UnsicentificLaLaLaLa/led-matrix/software/firmware/led-matrix_firmware/device/mm32g0001a.h

/*
 * Copyright 2023 MindMotion Microelectronics Co., Ltd.
 * All rights reserved.
 *
 * SPDX-License-Identifier: BSD-3-Clause
 */


#ifndef __MM32G0001A_H__
#define __MM32G0001A_H__

#ifdef __cplusplus
extern "C" {
#endif

/* -----------------------------------------------------------------------------
  -- Interrupt vector numbers
  ----------------------------------------------------------------------------- */

/*!
* @addtogroup Interrupt_vector_numbers Interrupt vector numbers

* @{
*/

/** Interrupt Number Definitions */

#define NUMBER_OF_INT_VECTORS 26                 /**< Number of interrupts in the Vector table */

typedef enum IRQ {
    Reset_IRQn                          = -15,                                   /*!< reset */
    NMI_IRQn                            = -14,                                   /*!< Non-Maskable Interrupt/RCC Clock Security System (CSS) connected to NMI vector */
    Hardwarefault_IRQn                  = -13,                                   /*!< All types of failures */
    SVCall_IRQn                         = -5,                                    /*!< System service calls via SWI instructions */
    DebugMonitor_IRQn                   = -4,                                    /*!< debug monitor */
    PendSV_IRQn                         = -2,                                    /*!< Suspendable system services */
    SysTick_IRQn                        = -1,                                    /*!< System tick timer */
    IWDG_IRQn                           = 0,                                     /*!< Watchdog interrupt (IWDG is EXTI17) */
    PVD_IRQn                            = 1,                                     /*!< Supply Voltage Detect (PVD) Interrupt (EXTI16) */
    FLASH_IRQn                          = 3,                                     /*!< Flash Global Interrupt */
    RCC_IRQn                            = 4,                                     /*!< RCC  global interrupt */
    EXTI0_1_IRQn                        = 5,                                     /*!< EXTI line [1: 0] interrupt */
    EXTI2_3_IRQn                        = 6,                                     /*!< EXTI line [3: 2] interrupt */
    EXTI4_15_IRQn                       = 7,                                     /*!< EXTI line [15: 4] interrupt */
    ADC1_IRQn                           = 12,                                    /*!< ADC1 global interrupt */
    TIM1_BRK_UP_TRG_COM_IRQn            = 13,                                    /*!< TIM1 brake, update, trigger, and COM interrupt */
    TIM1_CC_IRQn                        = 14,                                    /*!< TIM1 capture compare interrupt */
    TIM3_IRQn                           = 16,                                    /*!< TIM3 global interrupt */
    TIM14_IRQn                          = 19,                                    /*!< TIM14 global interrupt */
    I2C1_IRQn                           = 23,                                    /*!< I2C1 global interrupt */
    SPI1_IRQn                           = 25,                                    /*!< SPI1 global interrupt */
    USART1_IRQn                         = 27,                                    /*!< USART1 global interrupt */
    USART2_IRQn                         = 28,                                    /*!< USART2 global interrupt */

} IRQn_Type;

/*!

 * @}
 */ /* end of group Interrupt_vector_numbers */


/* -----------------------------------------------------------------------------
 -- Cortex M0 Core Configuration
  ----------------------------------------------------------------------------- */

/*!
 * @addtogroup Cortex_Core_Configuration Cortex M0 Core Configuration
 * @{
 */
#define __CM0_REV                 0x0000U   /* Core revision r0p0 */
#define __MPU_PRESENT             0U        /* no MPU present */
#define __VTOR_PRESENT            0U        /* no VTOR present */
#define __NVIC_PRIO_BITS          2U        /* Number of Bits used for Priority Levels */
#define __Vendor_SysTickConfig    0U        /* Set to 1 if different SysTick Config is used */

#include "core_cm0.h"                /* Core Peripheral Access Layer */

/*!
 * @}
 */ /* end of group Cortex_Core_Configuration */



/* -----------------------------------------------------------------------------
   -- Device Peripheral Access Layer
   ----------------------------------------------------------------------------- */

/*!
 * @addtogroup Peripheral_access_layer Device Peripheral Access Layer
 * @{

 */

/*
** Start of section using anonymous unions
*/

#if   defined (__CC_ARM)
  #pragma push
  #pragma anon_unions
#elif defined (__ICCARM__)
  #pragma language=extended
#elif defined(__ARMCC_VERSION) && (__ARMCC_VERSION >= 6010050)
  #pragma clang diagnostic push
  #pragma clang diagnostic ignored "-Wc11-extensions"
  #pragma clang diagnostic ignored "-Wreserved-id-macro"
#elif defined (__GNUC__)
  /* anonymous unions are enabled by default */
#else
  #warning Not supported compiler type
#endif

/* Define the base address of the large memory block mapping */

#define BOOT_BASE                   0x00000000u
#define FLASH_ADDR_BASE             0x08000000u
#define SYSTEMMEMORY_BASE           0x1FFFF400u
#define OPTIONBYTES_BASE            0x1FFFF800u
#define SRAM_BASE                   0x20000000u
#define APB1_0_BASE                 0x40000000u
#define APB1_1_BASE                 0x40010000u
#define AHB_0_BASE                  0x40020000u
#define AHB_1_BASE                  0x48000000u


/* Define the mapping base address of the peripheral module */
#define TIM3_BASE                   (APB1_0_BASE + 0x0400)
#define IWDG_BASE                   (APB1_0_BASE + 0x3000)
#define USART2_BASE                 (APB1_0_BASE + 0x4400)
#define I2C1_BASE                   (APB1_0_BASE + 0x5400)
#define PWR_BASE                    (APB1_0_BASE + 0x7000)

#define SYSCFG_BASE                 (APB1_1_BASE + 0x0000)
#define EXTI_BASE                   (APB1_1_BASE + 0x0400)
#define ADC1_BASE                   (APB1_1_BASE + 0x2400)
#define TIM1_BASE                   (APB1_1_BASE + 0x2C00)
#define SPI1_BASE                   (APB1_1_BASE + 0x3000)
#define DBGMCU_BASE                 (APB1_1_BASE + 0x3400)
#define USART1_BASE                 (APB1_1_BASE + 0x3800)
#define TIM14_BASE                  (APB1_1_BASE + 0x4000)

#define RCC_BASE                    (AHB_0_BASE + 0x1000)
#define FLASH_BASE                  (AHB_0_BASE + 0x2000)
#define CRC_BASE                    (AHB_0_BASE + 0x3000)

#define GPIOA_BASE                  (AHB_1_BASE + 0x0000)
#define GPIOB_BASE                  (AHB_1_BASE + 0x0400)



/*!
 * @addtogroup ADC_Peripheral_Access_Layer ADC Peripheral Access Layer
 *  @{
 */

/*******************************************************************************
 * ADC Type
 ******************************************************************************/
typedef struct {
    __IO uint32_t ADDATA;                                                         ///< Data register                                offset: 0x00
    __IO uint32_t ADCFG;                                                         ///< Configure register                           offset: 0x04
    __IO uint32_t ADCR;                                                           ///< Control register                             offset: 0x08
    __IO uint32_t Reserved0[1];                                                   ///< Reserved
    __IO uint32_t ADCMPR;                                                         ///< Compare register                             offset: 0x10
    __IO uint32_t ADSTA;                                                          ///< Status register                              offset: 0x14
    __IO uint32_t ADDR[9];                                                        ///< Channel data register                        offset: 0x18
    __IO uint32_t Reserved1[8];                                                   ///< Reserved
    __IO uint32_t CHANY0;                                                         ///< Arbitrary channel channel selection register 0offset: 0x5C
    __IO uint32_t CHANY1;                                                         ///< Arbitrary channel channel selection register 1offset: 0x60
    __IO uint32_t ANYCFG;                                                         ///< Arbitrary channel configuration register     offset: 0x64
    __IO uint32_t ANYCR;                                                          ///< Arbitrary channel control register           offset: 0x68
} ADC_Type;

/*!
 * @addtogroup ADC_Register_Masks Register Masks
 * @{ */

/*!
 * @brief ADC_ADDATA Register Bit Definition
 */

#define ADC_ADDATA_VALID_SHIFT                          (21)
#define ADC_ADDATA_VALID_MASK                           (0x01U << ADC_ADDATA_VALID_SHIFT)
#define ADC_ADDATA_VALID(x)                             (((uint32_t)(((uint32_t)(x)) << ADC_ADDATA_VALID_SHIFT)) & ADC_ADDATA_VALID_MASK)

#define ADC_ADDATA_OVERRUN_SHIFT                        (20)
#define ADC_ADDATA_OVERRUN_MASK                         (0x01U << ADC_ADDATA_OVERRUN_SHIFT)
#define ADC_ADDATA_OVERRUN(x)                           (((uint32_t)(((uint32_t)(x)) << ADC_ADDATA_OVERRUN_SHIFT)) & ADC_ADDATA_OVERRUN_MASK)

#define ADC_ADDATA_CHANNELSEL_SHIFT                     (16)
#define ADC_ADDATA_CHANNELSEL_MASK                      (0x0FU << ADC_ADDATA_CHANNELSEL_SHIFT)
#define ADC_ADDATA_CHANNELSEL(x)                        (((uint32_t)(((uint32_t)(x)) << ADC_ADDATA_CHANNELSEL_SHIFT)) & ADC_ADDATA_CHANNELSEL_MASK)

#define ADC_ADDATA_DATA_SHIFT                           (0)
#define ADC_ADDATA_DATA_MASK                            (0xFFFFU << ADC_ADDATA_DATA_SHIFT)
#define ADC_ADDATA_DATA(x)                              (((uint32_t)(((uint32_t)(x)) << ADC_ADDATA_DATA_SHIFT)) & ADC_ADDATA_DATA_MASK)

/*!
 * @brief ADC_ADCFG Register Bit Definition
 */

#define ADC_ADCFG_ADCPREL_SHIFT                        (14)
#define ADC_ADCFG_ADCPREL_MASK                         (0x01U << ADC_ADCFG_ADCPREL_SHIFT)
#define ADC_ADCFG_ADCPREL(x)                           (((uint32_t)(((uint32_t)(x)) << ADC_ADCFG_ADCPREL_SHIFT)) & ADC_ADCFG_ADCPREL_MASK)

#define ADC_ADCFG_SAMCTL_SHIFT                         (10)
#define ADC_ADCFG_SAMCTL_MASK                          (0x0FU << ADC_ADCFG_SAMCTL_SHIFT)
#define ADC_ADCFG_SAMCTL(x)                            (((uint32_t)(((uint32_t)(x)) << ADC_ADCFG_SAMCTL_SHIFT)) & ADC_ADCFG_SAMCTL_MASK)

#define ADC_ADCFG_RSLTCTL_SHIFT                        (7)
#define ADC_ADCFG_RSLTCTL_MASK                         (0x07U << ADC_ADCFG_RSLTCTL_SHIFT)
#define ADC_ADCFG_RSLTCTL(x)                           (((uint32_t)(((uint32_t)(x)) << ADC_ADCFG_RSLTCTL_SHIFT)) & ADC_ADCFG_RSLTCTL_MASK)

#define ADC_ADCFG_ADCPREH_SHIFT                        (4)
#define ADC_ADCFG_ADCPREH_MASK                         (0x07U << ADC_ADCFG_ADCPREH_SHIFT)
#define ADC_ADCFG_ADCPREH(x)                           (((uint32_t)(((uint32_t)(x)) << ADC_ADCFG_ADCPREH_SHIFT)) & ADC_ADCFG_ADCPREH_MASK)

#define ADC_ADCFG_VSEN_SHIFT                           (3)
#define ADC_ADCFG_VSEN_MASK                            (0x01U << ADC_ADCFG_VSEN_SHIFT)
#define ADC_ADCFG_VSEN(x)                              (((uint32_t)(((uint32_t)(x)) << ADC_ADCFG_VSEN_SHIFT)) & ADC_ADCFG_VSEN_MASK)

#define ADC_ADCFG_AWDEN_SHIFT                          (1)
#define ADC_ADCFG_AWDEN_MASK                           (0x01U << ADC_ADCFG_AWDEN_SHIFT)
#define ADC_ADCFG_AWDEN(x)                             (((uint32_t)(((uint32_t)(x)) << ADC_ADCFG_AWDEN_SHIFT)) & ADC_ADCFG_AWDEN_MASK)

#define ADC_ADCFG_ADEN_SHIFT                           (0)
#define ADC_ADCFG_ADEN_MASK                            (0x01U << ADC_ADCFG_ADEN_SHIFT)
#define ADC_ADCFG_ADEN(x)                              (((uint32_t)(((uint32_t)(x)) << ADC_ADCFG_ADEN_SHIFT)) & ADC_ADCFG_ADEN_MASK)

/*!
 * @brief ADC_ADCR Register Bit Definition
 */

#define ADC_ADCR_TRGEDGE_SHIFT                          (24)
#define ADC_ADCR_TRGEDGE_MASK                           (0x03U << ADC_ADCR_TRGEDGE_SHIFT)
#define ADC_ADCR_TRGEDGE(x)                             (((uint32_t)(((uint32_t)(x)) << ADC_ADCR_TRGEDGE_SHIFT)) & ADC_ADCR_TRGEDGE_MASK)

#define ADC_ADCR_TRGSHIFT_SHIFT                         (19)
#define ADC_ADCR_TRGSHIFT_MASK                          (0x07U << ADC_ADCR_TRGSHIFT_SHIFT)
#define ADC_ADCR_TRGSHIFT(x)                            (((uint32_t)(((uint32_t)(x)) << ADC_ADCR_TRGSHIFT_SHIFT)) & ADC_ADCR_TRGSHIFT_MASK)

#define ADC_ADCR_TRGSELH_SHIFT                          (17)
#define ADC_ADCR_TRGSELH_MASK                           (0x03U << ADC_ADCR_TRGSELH_SHIFT)
#define ADC_ADCR_TRGSELH(x)                             (((uint32_t)(((uint32_t)(x)) << ADC_ADCR_TRGSELH_SHIFT)) & ADC_ADCR_TRGSELH_MASK)

#define ADC_ADCR_CMPCH_SHIFT                            (12)
#define ADC_ADCR_CMPCH_MASK                             (0x0FU << ADC_ADCR_CMPCH_SHIFT)
#define ADC_ADCR_CMPCH(x)                               (((uint32_t)(((uint32_t)(x)) << ADC_ADCR_CMPCH_SHIFT)) & ADC_ADCR_CMPCH_MASK)

#define ADC_ADCR_ALIGN_SHIFT                            (11)
#define ADC_ADCR_ALIGN_MASK                             (0x01U << ADC_ADCR_ALIGN_SHIFT)
#define ADC_ADCR_ALIGN(x)                               (((uint32_t)(((uint32_t)(x)) << ADC_ADCR_ALIGN_SHIFT)) & ADC_ADCR_ALIGN_MASK)

#define ADC_ADCR_ADMD_SHIFT                             (9)
#define ADC_ADCR_ADMD_MASK                              (0x03U << ADC_ADCR_ADMD_SHIFT)
#define ADC_ADCR_ADMD(x)                                (((uint32_t)(((uint32_t)(x)) << ADC_ADCR_ADMD_SHIFT)) & ADC_ADCR_ADMD_MASK)

#define ADC_ADCR_ADST_SHIFT                             (8)
#define ADC_ADCR_ADST_MASK                              (0x01U << ADC_ADCR_ADST_SHIFT)
#define ADC_ADCR_ADST(x)                                (((uint32_t)(((uint32_t)(x)) << ADC_ADCR_ADST_SHIFT)) & ADC_ADCR_ADST_MASK)

#define ADC_ADCR_TRGSELL_SHIFT                          (4)
#define ADC_ADCR_TRGSELL_MASK                           (0x07U << ADC_ADCR_TRGSELL_SHIFT)
#define ADC_ADCR_TRGSELL(x)                             (((uint32_t)(((uint32_t)(x)) << ADC_ADCR_TRGSELL_SHIFT)) & ADC_ADCR_TRGSELL_MASK)

#define ADC_ADCR_TRGEN_SHIFT                            (2)
#define ADC_ADCR_TRGEN_MASK                             (0x01U << ADC_ADCR_TRGEN_SHIFT)
#define ADC_ADCR_TRGEN(x)                               (((uint32_t)(((uint32_t)(x)) << ADC_ADCR_TRGEN_SHIFT)) & ADC_ADCR_TRGEN_MASK)

#define ADC_ADCR_AWDIE_SHIFT                            (1)
#define ADC_ADCR_AWDIE_MASK                             (0x01U << ADC_ADCR_AWDIE_SHIFT)
#define ADC_ADCR_AWDIE(x)                               (((uint32_t)(((uint32_t)(x)) << ADC_ADCR_AWDIE_SHIFT)) & ADC_ADCR_AWDIE_MASK)

#define ADC_ADCR_ADIE_SHIFT                             (0)
#define ADC_ADCR_ADIE_MASK                              (0x01U << ADC_ADCR_ADIE_SHIFT)
#define ADC_ADCR_ADIE(x)                                (((uint32_t)(((uint32_t)(x)) << ADC_ADCR_ADIE_SHIFT)) & ADC_ADCR_ADIE_MASK)

/*!
 * @brief ADC_ADCMPR Register Bit Definition
 */

#define ADC_ADCMPR_CMPHDATA_SHIFT                       (16)
#define ADC_ADCMPR_CMPHDATA_MASK                        (0xFFFU << ADC_ADCMPR_CMPHDATA_SHIFT)
#define ADC_ADCMPR_CMPHDATA(x)                          (((uint32_t)(((uint32_t)(x)) << ADC_ADCMPR_CMPHDATA_SHIFT)) & ADC_ADCMPR_CMPHDATA_MASK)

#define ADC_ADCMPR_CMPLDATA_SHIFT                       (0)
#define ADC_ADCMPR_CMPLDATA_MASK                        (0xFFFU << ADC_ADCMPR_CMPLDATA_SHIFT)
#define ADC_ADCMPR_CMPLDATA(x)                          (((uint32_t)(((uint32_t)(x)) << ADC_ADCMPR_CMPLDATA_SHIFT)) & ADC_ADCMPR_CMPLDATA_MASK)

/*!
 * @brief ADC_ADSTA Register Bit Definition
 */

#define ADC_ADSTA_OVERRUN_SHIFT                         (20)
#define ADC_ADSTA_OVERRUN_MASK                          (0x3FFU << ADC_ADSTA_OVERRUN_SHIFT)
#define ADC_ADSTA_OVERRUN(x)                            (((uint32_t)(((uint32_t)(x)) << ADC_ADSTA_OVERRUN_SHIFT)) & ADC_ADSTA_OVERRUN_MASK)

#define ADC_ADSTA_VALID_SHIFT                           (8)
#define ADC_ADSTA_VALID_MASK                            (0x1FFU << ADC_ADSTA_VALID_SHIFT)
#define ADC_ADSTA_VALID(x)                              (((uint32_t)(((uint32_t)(x)) << ADC_ADSTA_VALID_SHIFT)) & ADC_ADSTA_VALID_MASK)

#define ADC_ADSTA_CH_SHIFT                              (4)
#define ADC_ADSTA_CH_MASK                               (0x0FU << ADC_ADSTA_CH_SHIFT)
#define ADC_ADSTA_CH(x)                                 (((uint32_t)(((uint32_t)(x)) << ADC_ADSTA_CH_SHIFT)) & ADC_ADSTA_CH_MASK)

#define ADC_ADSTA_BUSY_SHIFT                            (2)
#define ADC_ADSTA_BUSY_MASK                             (0x01U << ADC_ADSTA_BUSY_SHIFT)
#define ADC_ADSTA_BUSY(x)                               (((uint32_t)(((uint32_t)(x)) << ADC_ADSTA_BUSY_SHIFT)) & ADC_ADSTA_BUSY_MASK)

#define ADC_ADSTA_AWDIF_SHIFT                           (1)
#define ADC_ADSTA_AWDIF_MASK                            (0x01U << ADC_ADSTA_AWDIF_SHIFT)
#define ADC_ADSTA_AWDIF(x)                              (((uint32_t)(((uint32_t)(x)) << ADC_ADSTA_AWDIF_SHIFT)) & ADC_ADSTA_AWDIF_MASK)

#define ADC_ADSTA_ADIF_SHIFT                            (0)
#define ADC_ADSTA_ADIF_MASK                             (0x01U << ADC_ADSTA_ADIF_SHIFT)
#define ADC_ADSTA_ADIF(x)                               (((uint32_t)(((uint32_t)(x)) << ADC_ADSTA_ADIF_SHIFT)) & ADC_ADSTA_ADIF_MASK)

/*!
 * @brief ADC_ADDR Register Bit Definition
 */

#define ADC_ADDR_VALID_SHIFT                            (21)
#define ADC_ADDR_VALID_MASK                             (0x01U << ADC_ADDR_VALID_SHIFT)
#define ADC_ADDR_VALID(x)                               (((uint32_t)(((uint32_t)(x)) << ADC_ADDR_VALID_SHIFT)) & ADC_ADDR_VALID_MASK)
#define ADC_ADDR_OVERRUN_SHIFT                          (20)
#define ADC_ADDR_OVERRUN_MASK                           (0x01U << ADC_ADDR_OVERRUN_SHIFT)
#define ADC_ADDR_OVERRUN(x)                             (((uint32_t)(((uint32_t)(x)) << ADC_ADDR_OVERRUN_SHIFT)) & ADC_ADDR_OVERRUN_MASK)
#define ADC_ADDR_DATA_SHIFT                             (0)
#define ADC_ADDR_DATA_MASK                              (0xFFFFU << ADC_ADDR_DATA_SHIFT)
#define ADC_ADDR_DATA(x)                                (((uint32_t)(((uint32_t)(x)) << ADC_ADDR_DATA_SHIFT)) & ADC_ADDR_DATA_MASK)

/*!
 * @brief ADC_CHANY0 Register Bit Definition
 */

#define ADC_CHANY0_CHANYSEL7_SHIFT                      (28)
#define ADC_CHANY0_CHANYSEL7_MASK                       (0x0FU << ADC_CHANY0_CHANYSEL7_SHIFT)
#define ADC_CHANY0_CHANYSEL7(x)                         (((uint32_t)(((uint32_t)(x)) << ADC_CHANY0_CHANYSEL7_SHIFT)) & ADC_CHANY0_CHANYSEL7_MASK)

#define ADC_CHANY0_CHANYSEL6_SHIFT                      (24)
#define ADC_CHANY0_CHANYSEL6_MASK                       (0x0FU << ADC_CHANY0_CHANYSEL6_SHIFT)
#define ADC_CHANY0_CHANYSEL6(x)                         (((uint32_t)(((uint32_t)(x)) << ADC_CHANY0_CHANYSEL6_SHIFT)) & ADC_CHANY0_CHANYSEL6_MASK)

#define ADC_CHANY0_CHANYSEL5_SHIFT                      (20)
#define ADC_CHANY0_CHANYSEL5_MASK                       (0x0FU << ADC_CHANY0_CHANYSEL5_SHIFT)
#define ADC_CHANY0_CHANYSEL5(x)                         (((uint32_t)(((uint32_t)(x)) << ADC_CHANY0_CHANYSEL5_SHIFT)) & ADC_CHANY0_CHANYSEL5_MASK)

#define ADC_CHANY0_CHANYSEL4_SHIFT                      (16)
#define ADC_CHANY0_CHANYSEL4_MASK                       (0x0FU << ADC_CHANY0_CHANYSEL4_SHIFT)
#define ADC_CHANY0_CHANYSEL4(x)                         (((uint32_t)(((uint32_t)(x)) << ADC_CHANY0_CHANYSEL4_SHIFT)) & ADC_CHANY0_CHANYSEL4_MASK)

#define ADC_CHANY0_CHANYSEL3_SHIFT                      (12)
#define ADC_CHANY0_CHANYSEL3_MASK                       (0x0FU << ADC_CHANY0_CHANYSEL3_SHIFT)
#define ADC_CHANY0_CHANYSEL3(x)                         (((uint32_t)(((uint32_t)(x)) << ADC_CHANY0_CHANYSEL3_SHIFT)) & ADC_CHANY0_CHANYSEL3_MASK)

#define ADC_CHANY0_CHANYSEL2_SHIFT                      (8)
#define ADC_CHANY0_CHANYSEL2_MASK                       (0x0FU << ADC_CHANY0_CHANYSEL2_SHIFT)
#define ADC_CHANY0_CHANYSEL2(x)                         (((uint32_t)(((uint32_t)(x)) << ADC_CHANY0_CHANYSEL2_SHIFT)) & ADC_CHANY0_CHANYSEL2_MASK)

#define ADC_CHANY0_CHANYSEL1_SHIFT                      (4)
#define ADC_CHANY0_CHANYSEL1_MASK                       (0x0FU << ADC_CHANY0_CHANYSEL1_SHIFT)
#define ADC_CHANY0_CHANYSEL1(x)                         (((uint32_t)(((uint32_t)(x)) << ADC_CHANY0_CHANYSEL1_SHIFT)) & ADC_CHANY0_CHANYSEL1_MASK)

#define ADC_CHANY0_CHANYSEL0_SHIFT                      (0)
#define ADC_CHANY0_CHANYSEL0_MASK                       (0x0FU << ADC_CHANY0_CHANYSEL0_SHIFT)
#define ADC_CHANY0_CHANYSEL0(x)                         (((uint32_t)(((uint32_t)(x)) << ADC_CHANY0_CHANYSEL0_SHIFT)) & ADC_CHANY0_CHANYSEL0_MASK)

/*!
 * @brief ADC_CHANY1 Register Bit Definition
 */

#define ADC_CHANY1_CHANYSEL8_SHIFT                      (0)
#define ADC_CHANY1_CHANYSEL8_MASK                       (0x0FU << ADC_CHANY1_CHANYSEL8_SHIFT)
#define ADC_CHANY1_CHANYSEL8(x)                         (((uint32_t)(((uint32_t)(x)) << ADC_CHANY1_CHANYSEL8_SHIFT)) & ADC_CHANY1_CHANYSEL8_MASK)

/*!
 * @brief ADC_ANYCFG Register Bit Definition
 */

#define ADC_ANYCFG_CHANYNUM_SHIFT                      (0)
#define ADC_ANYCFG_CHANYNUM_MASK                       (0x0FU << ADC_ANYCFG_CHANYNUM_SHIFT)
#define ADC_ANYCFG_CHANYNUM(x)                         (((uint32_t)(((uint32_t)(x)) << ADC_ANYCFG_CHANYNUM_SHIFT)) & ADC_ANYCFG_CHANYNUM_MASK)

/*!
 * @brief ADC_ANYCR Register Bit Definition
 */

#define ADC_ANYCR_CHANYMDEN_SHIFT                      (0)
#define ADC_ANYCR_CHANYMDEN_MASK                       (0x01U << ADC_ANYCR_CHANYMDEN_SHIFT)
#define ADC_ANYCR_CHANYMDEN(x)                         (((uint32_t)(((uint32_t)(x)) << ADC_ANYCR_CHANYMDEN_SHIFT)) & ADC_ANYCR_CHANYMDEN_MASK)

/*!
 * @}
 */ /* end of group ADC_Register_Masks */
/******************************************************************************
 * ADC Instance
 ******************************************************************************/

#define ADC1                ((ADC_Type*)ADC1_BASE)

/*!
 * @}
 */ /* end of group ADC_Peripheral_Access_Layer */

/*!
 * @addtogroup CRC_Peripheral_Access_Layer CRC Peripheral Access Layer
 *  @{
 */

/*******************************************************************************
 * CRC Type
 ******************************************************************************/
typedef struct {
    __IO uint32_t DR;                                                             ///< Data register                                offset: 0x00
    __IO uint32_t IDR;                                                            ///< Independent data register                    offset: 0x04
    __IO uint32_t CTRL;                                                           ///< Control register                             offset: 0x08
} CRC_Type;

/*!
 * @addtogroup CRC_Register_Masks Register Masks
 * @{ */

/*!
 * @brief CRC_DR Register Bit Definition
 */

#define CRC_DR_DR_SHIFT                                 (0)
#define CRC_DR_DR_MASK                                  (0xFFFFFFFFU << CRC_DR_DR_SHIFT)
#define CRC_DR_DR(x)                                    (((uint32_t)(((uint32_t)(x)) << CRC_DR_DR_SHIFT)) & CRC_DR_DR_MASK)

/*!
 * @brief CRC_IDR Register Bit Definition
 */

#define CRC_IDR_IDR_SHIFT                               (0)
#define CRC_IDR_IDR_MASK                                (0xFFU << CRC_IDR_IDR_SHIFT)
#define CRC_IDR_IDR(x)                                  (((uint32_t)(((uint32_t)(x)) << CRC_IDR_IDR_SHIFT)) & CRC_IDR_IDR_MASK)

/*!
 * @brief CRC_CTRL Register Bit Definition
 */

#define CRC_CTRL_RESET_SHIFT                            (0)
#define CRC_CTRL_RESET_MASK                             (0x01U << CRC_CTRL_RESET_SHIFT)
#define CRC_CTRL_RESET(x)                               (((uint32_t)(((uint32_t)(x)) << CRC_CTRL_RESET_SHIFT)) & CRC_CTRL_RESET_MASK)

/*!
 * @}
 */ /* end of group CRC_Register_Masks */
/******************************************************************************
 * CRC Instance
 ******************************************************************************/

#define CRC                ((CRC_Type*)CRC_BASE)

/*!
 * @}
 */ /* end of group CRC_Peripheral_Access_Layer */

/*!
 * @addtogroup DBGMCU_Peripheral_Access_Layer DBG Peripheral Access Layer
 *  @{
 */

/*******************************************************************************
 * DBGMCU Type
 ******************************************************************************/
typedef struct {
    __IO uint32_t IDCODE;                                                         ///< ID CODE                                      offset: 0x00
    __IO uint32_t CR;                                                             ///< Control Register                             offset: 0x04
} DBGMCU_Type;

/*!
 * @addtogroup DBGMCU_Register_Masks Register Masks
 * @{ */

/*!
 * @brief DBGMCU_IDCODE Register Bit Definition
 */

#define DBGMCU_IDCODE_DEVID_SHIFT                          (0)
#define DBGMCU_IDCODE_DEVID_MASK                           (0xFFFFFFFFU << DBGMCU_IDCODE_DEVID_SHIFT)
#define DBGMCU_IDCODE_DEVID(x)                             (((uint32_t)(((uint32_t)(x)) << DBGMCU_IDCODE_DEVID_SHIFT)) & DBGMCU_IDCODE_DEVID_MASK)

/*!
 * @brief DBGMCU_CR Register Bit Definition
 */

#define DBGMCU_CR_DBGTIM14STOP_SHIFT                       (18)
#define DBGMCU_CR_DBGTIM14STOP_MASK                        (0x01U << DBGMCU_CR_DBGTIM14STOP_SHIFT)
#define DBGMCU_CR_DBGTIM14STOP(x)                          (((uint32_t)(((uint32_t)(x)) << DBGMCU_CR_DBGTIM14STOP_SHIFT)) & DBGMCU_CR_DBGTIM14STOP_MASK)

#define DBGMCU_CR_DBGTIM3PWMOFF_SHIFT                      (15)
#define DBGMCU_CR_DBGTIM3PWMOFF_MASK                       (0x01U << DBGMCU_CR_DBGTIM3PWMOFF_SHIFT)
#define DBGMCU_CR_DBGTIM3PWMOFF(x)                         (((uint32_t)(((uint32_t)(x)) << DBGMCU_CR_DBGTIM3PWMOFF_SHIFT)) & DBGMCU_CR_DBGTIM3PWMOFF_MASK)

#define DBGMCU_CR_DBGTIM1PWMOFF_SHIFT                      (13)
#define DBGMCU_CR_DBGTIM1PWMOFF_MASK                       (0x01U << DBGMCU_CR_DBGTIM1PWMOFF_SHIFT)
#define DBGMCU_CR_DBGTIM1PWMOFF(x)                         (((uint32_t)(((uint32_t)(x)) << DBGMCU_CR_DBGTIM1PWMOFF_SHIFT)) & DBGMCU_CR_DBGTIM1PWMOFF_MASK)

#define DBGMCU_CR_DBGTIM3STOP_SHIFT                        (12)
#define DBGMCU_CR_DBGTIM3STOP_MASK                         (0x01U << DBGMCU_CR_DBGTIM3STOP_SHIFT)
#define DBGMCU_CR_DBGTIM3STOP(x)                           (((uint32_t)(((uint32_t)(x)) << DBGMCU_CR_DBGTIM3STOP_SHIFT)) & DBGMCU_CR_DBGTIM3STOP_MASK)

#define DBGMCU_CR_DBGTIM1STOP_SHIFT                        (10)
#define DBGMCU_CR_DBGTIM1STOP_MASK                         (0x01U << DBGMCU_CR_DBGTIM1STOP_SHIFT)
#define DBGMCU_CR_DBGTIM1STOP(x)                           (((uint32_t)(((uint32_t)(x)) << DBGMCU_CR_DBGTIM1STOP_SHIFT)) & DBGMCU_CR_DBGTIM1STOP_MASK)

#define DBGMCU_CR_DBGIWDGSTOP_SHIFT                        (8)
#define DBGMCU_CR_DBGIWDGSTOP_MASK                         (0x01U << DBGMCU_CR_DBGIWDGSTOP_SHIFT)
#define DBGMCU_CR_DBGIWDGSTOP(x)                           (((uint32_t)(((uint32_t)(x)) << DBGMCU_CR_DBGIWDGSTOP_SHIFT)) & DBGMCU_CR_DBGIWDGSTOP_MASK)

#define DBGMCU_CR_DBGSTOPFORLDO_SHIFT                      (3)
#define DBGMCU_CR_DBGSTOPFORLDO_MASK                       (0x01U << DBGMCU_CR_DBGSTOPFORLDO_SHIFT)
#define DBGMCU_CR_DBGSTOPFORLDO(x)                         (((uint32_t)(((uint32_t)(x)) << DBGMCU_CR_DBGSTOPFORLDO_SHIFT)) & DBGMCU_CR_DBGSTOPFORLDO_MASK)

#define DBGMCU_CR_DBGSTOP_SHIFT                            (1)
#define DBGMCU_CR_DBGSTOP_MASK                             (0x01U << DBGMCU_CR_DBGSTOP_SHIFT)
#define DBGMCU_CR_DBGSTOP(x)                               (((uint32_t)(((uint32_t)(x)) << DBGMCU_CR_DBGSTOP_SHIFT)) & DBGMCU_CR_DBGSTOP_MASK)

#define DBGMCU_CR_DBGSLEEP_SHIFT                           (0)
#define DBGMCU_CR_DBGSLEEP_MASK                            (0x01U << DBGMCU_CR_DBGSLEEP_SHIFT)
#define DBGMCU_CR_DBGSLEEP(x)                              (((uint32_t)(((uint32_t)(x)) << DBGMCU_CR_DBGSLEEP_SHIFT)) & DBGMCU_CR_DBGSLEEP_MASK)

/*!
 * @}
 */ /* end of group DBGMCU_Register_Masks */
/******************************************************************************
 * DBGMCU Instance
 ******************************************************************************/

#define DBGMCU                ((DBGMCU_Type*)DBGMCU_BASE)

/*!
 * @}
 */ /* end of group DBGMCU_Peripheral_Access_Layer */

/*!
 * @addtogroup DEVICE_Peripheral_Access_Layer DEVICE Peripheral Access Layer
 *  @{
 */

/*******************************************************************************
 * DEVICE Type
 ******************************************************************************/
typedef struct {
    __IO uint32_t UID1;                                                           ///< Configuration register                       offset: 0x00
    __IO uint32_t UID2;                                                           ///< Configuration register                       offset: 0x04
    __IO uint32_t UID3;                                                           ///< Configuration register                       offset: 0x08
} DEVICE_Type;

/*!
 * @addtogroup DEVICE_Register_Masks Register Masks
 * @{ */

/*!
 * @brief DEVICE_UID1 Register Bit Definition
 */

#define DEVICE_UID1_UID_SHIFT                           (0)
#define DEVICE_UID1_UID_MASK                            (0xFFFFFFFFU << DEVICE_UID1_UID_SHIFT)
#define DEVICE_UID1_UID(x)                              (((uint32_t)(((uint32_t)(x)) << DEVICE_UID1_UID_SHIFT)) & DEVICE_UID1_UID_MASK)

/*!
 * @brief DEVICE_UID2 Register Bit Definition
 */

#define DEVICE_UID2_UID_SHIFT                           (0)
#define DEVICE_UID2_UID_MASK                            (0xFFFFFFFFU << DEVICE_UID2_UID_SHIFT)
#define DEVICE_UID2_UID(x)                              (((uint32_t)(((uint32_t)(x)) << DEVICE_UID2_UID_SHIFT)) & DEVICE_UID2_UID_MASK)

/*!
 * @brief DEVICE_UID3 Register Bit Definition
 */

#define DEVICE_UID3_UID_SHIFT                           (0)
#define DEVICE_UID3_UID_MASK                            (0xFFFFFFFFU << DEVICE_UID3_UID_SHIFT)
#define DEVICE_UID3_UID(x)                              (((uint32_t)(((uint32_t)(x)) << DEVICE_UID3_UID_SHIFT)) & DEVICE_UID3_UID_MASK)

/*!
 * @}
 */ /* end of group DEVICE_Register_Masks */
/******************************************************************************
 * DEVICE Instance
 ******************************************************************************/

#define DEVICE                ((DEVICE_Type*)DEVICE_BASE)

/*!
 * @}
 */ /* end of group DEVICE_Peripheral_Access_Layer */

/*!
 * @addtogroup SYSCFG_Peripheral_Access_Layer SYSCFG Peripheral Access Layer
 *  @{
 */

/*******************************************************************************
 * SYSCFG Type
 ******************************************************************************/
typedef struct {
    __IO uint32_t CFGR;                                                           ///< Configuration register                       offset: 0x00
    __IO uint32_t Reserved0[1];                                                   ///< Reserved
    __IO uint32_t EXTICR1;                                                        ///< External interrupt configuration register 1  offset: 0x08
    __IO uint32_t EXTICR2;                                                        ///< External interrupt configuration register 2  offset: 0x0C
    __IO uint32_t EXTICR3;                                                        ///< External interrupt configuration register 3  offset: 0x10
    __IO uint32_t EXTICR4;                                                        ///< External interrupt configuration register 4  offset: 0x14
    __IO uint32_t PADHYS;                                                         ///< PAD configuration register                   offset: 0x18
} SYSCFG_Type;

/*!
 * @addtogroup SYSCFG_Register_Masks Register Masks
 * @{ */

/*!
 * @brief SYSCFG_CFGR Register Bit Definition
 */

#define SYSCFG_CFGR_MEMMODE_SHIFT                       (0)
#define SYSCFG_CFGR_MEMMODE_MASK                        (0x03U << SYSCFG_CFGR_MEMMODE_SHIFT)
#define SYSCFG_CFGR_MEMMODE(x)                          (((uint32_t)(((uint32_t)(x)) << SYSCFG_CFGR_MEMMODE_SHIFT)) & SYSCFG_CFGR_MEMMODE_MASK)

/*!
 * @brief SYSCFG_EXTICR1 Register Bit Definition
 */

#define SYSCFG_EXTICR1_EXTI3_SHIFT                      (12)
#define SYSCFG_EXTICR1_EXTI3_MASK                       (0x0FU << SYSCFG_EXTICR1_EXTI3_SHIFT)
#define SYSCFG_EXTICR1_EXTI3(x)                         (((uint32_t)(((uint32_t)(x)) << SYSCFG_EXTICR1_EXTI3_SHIFT)) & SYSCFG_EXTICR1_EXTI3_MASK)

#define SYSCFG_EXTICR1_EXTI2_SHIFT                      (8)
#define SYSCFG_EXTICR1_EXTI2_MASK                       (0x0FU << SYSCFG_EXTICR1_EXTI2_SHIFT)
#define SYSCFG_EXTICR1_EXTI2(x)                         (((uint32_t)(((uint32_t)(x)) << SYSCFG_EXTICR1_EXTI2_SHIFT)) & SYSCFG_EXTICR1_EXTI2_MASK)

#define SYSCFG_EXTICR1_EXTI1_SHIFT                      (4)
#define SYSCFG_EXTICR1_EXTI1_MASK                       (0x0FU << SYSCFG_EXTICR1_EXTI1_SHIFT)
#define SYSCFG_EXTICR1_EXTI1(x)                         (((uint32_t)(((uint32_t)(x)) << SYSCFG_EXTICR1_EXTI1_SHIFT)) & SYSCFG_EXTICR1_EXTI1_MASK)

#define SYSCFG_EXTICR1_EXTI0_SHIFT                      (0)
#define SYSCFG_EXTICR1_EXTI0_MASK                       (0x0FU << SYSCFG_EXTICR1_EXTI0_SHIFT)
#define SYSCFG_EXTICR1_EXTI0(x)                         (((uint32_t)(((uint32_t)(x)) << SYSCFG_EXTICR1_EXTI0_SHIFT)) & SYSCFG_EXTICR1_EXTI0_MASK)

/*!
 * @brief SYSCFG_EXTICR2 Register Bit Definition
 */

#define SYSCFG_EXTICR2_EXTI7_SHIFT                      (12)
#define SYSCFG_EXTICR2_EXTI7_MASK                       (0x0FU << SYSCFG_EXTICR2_EXTI7_SHIFT)
#define SYSCFG_EXTICR2_EXTI7(x)                         (((uint32_t)(((uint32_t)(x)) << SYSCFG_EXTICR2_EXTI7_SHIFT)) & SYSCFG_EXTICR2_EXTI7_MASK)

#define SYSCFG_EXTICR2_EXTI6_SHIFT                      (8)
#define SYSCFG_EXTICR2_EXTI6_MASK                       (0x0FU << SYSCFG_EXTICR2_EXTI6_SHIFT)
#define SYSCFG_EXTICR2_EXTI6(x)                         (((uint32_t)(((uint32_t)(x)) << SYSCFG_EXTICR2_EXTI6_SHIFT)) & SYSCFG_EXTICR2_EXTI6_MASK)

#define SYSCFG_EXTICR2_EXTI5_SHIFT                      (4)
#define SYSCFG_EXTICR2_EXTI5_MASK                       (0x0FU << SYSCFG_EXTICR2_EXTI5_SHIFT)
#define SYSCFG_EXTICR2_EXTI5(x)                         (((uint32_t)(((uint32_t)(x)) << SYSCFG_EXTICR2_EXTI5_SHIFT)) & SYSCFG_EXTICR2_EXTI5_MASK)

#define SYSCFG_EXTICR2_EXTI4_SHIFT                      (0)
#define SYSCFG_EXTICR2_EXTI4_MASK                       (0x0FU << SYSCFG_EXTICR2_EXTI4_SHIFT)
#define SYSCFG_EXTICR2_EXTI4(x)                         (((uint32_t)(((uint32_t)(x)) << SYSCFG_EXTICR2_EXTI4_SHIFT)) & SYSCFG_EXTICR2_EXTI4_MASK)

/*!
 * @brief SYSCFG_EXTICR3 Register Bit Definition
 */

#define SYSCFG_EXTICR3_EXTI11_SHIFT                     (12)
#define SYSCFG_EXTICR3_EXTI11_MASK                      (0x0FU << SYSCFG_EXTICR3_EXTI11_SHIFT)
#define SYSCFG_EXTICR3_EXTI11(x)                        (((uint32_t)(((uint32_t)(x)) << SYSCFG_EXTICR3_EXTI11_SHIFT)) & SYSCFG_EXTICR3_EXTI11_MASK)

#define SYSCFG_EXTICR3_EXTI10_SHIFT                     (8)
#define SYSCFG_EXTICR3_EXTI10_MASK                      (0x0FU << SYSCFG_EXTICR3_EXTI10_SHIFT)
#define SYSCFG_EXTICR3_EXTI10(x)                        (((uint32_t)(((uint32_t)(x)) << SYSCFG_EXTICR3_EXTI10_SHIFT)) & SYSCFG_EXTICR3_EXTI10_MASK)

#define SYSCFG_EXTICR3_EXTI9_SHIFT                      (4)
#define SYSCFG_EXTICR3_EXTI9_MASK                       (0x0FU << SYSCFG_EXTICR3_EXTI9_SHIFT)
#define SYSCFG_EXTICR3_EXTI9(x)                         (((uint32_t)(((uint32_t)(x)) << SYSCFG_EXTICR3_EXTI9_SHIFT)) & SYSCFG_EXTICR3_EXTI9_MASK)

#define SYSCFG_EXTICR3_EXTI8_SHIFT                      (0)
#define SYSCFG_EXTICR3_EXTI8_MASK                       (0x0FU << SYSCFG_EXTICR3_EXTI8_SHIFT)
#define SYSCFG_EXTICR3_EXTI8(x)                         (((uint32_t)(((uint32_t)(x)) << SYSCFG_EXTICR3_EXTI8_SHIFT)) & SYSCFG_EXTICR3_EXTI8_MASK)

/*!
 * @brief SYSCFG_EXTICR4 Register Bit Definition
 */

#define SYSCFG_EXTICR4_EXTI15_SHIFT                     (12)
#define SYSCFG_EXTICR4_EXTI15_MASK                      (0x0FU << SYSCFG_EXTICR4_EXTI15_SHIFT)
#define SYSCFG_EXTICR4_EXTI15(x)                        (((uint32_t)(((uint32_t)(x)) << SYSCFG_EXTICR4_EXTI15_SHIFT)) & SYSCFG_EXTICR4_EXTI15_MASK)

#define SYSCFG_EXTICR4_EXTI14_SHIFT                     (8)
#define SYSCFG_EXTICR4_EXTI14_MASK                      (0x0FU << SYSCFG_EXTICR4_EXTI14_SHIFT)
#define SYSCFG_EXTICR4_EXTI14(x)                        (((uint32_t)(((uint32_t)(x)) << SYSCFG_EXTICR4_EXTI14_SHIFT)) & SYSCFG_EXTICR4_EXTI14_MASK)

#define SYSCFG_EXTICR4_EXTI13_SHIFT                     (4)
#define SYSCFG_EXTICR4_EXTI13_MASK                      (0x0FU << SYSCFG_EXTICR4_EXTI13_SHIFT)
#define SYSCFG_EXTICR4_EXTI13(x)                        (((uint32_t)(((uint32_t)(x)) << SYSCFG_EXTICR4_EXTI13_SHIFT)) & SYSCFG_EXTICR4_EXTI13_MASK)

#define SYSCFG_EXTICR4_EXTI12_SHIFT                     (0)
#define SYSCFG_EXTICR4_EXTI12_MASK                      (0x0FU << SYSCFG_EXTICR4_EXTI12_SHIFT)
#define SYSCFG_EXTICR4_EXTI12(x)                        (((uint32_t)(((uint32_t)(x)) << SYSCFG_EXTICR4_EXTI12_SHIFT)) & SYSCFG_EXTICR4_EXTI12_MASK)

/*!
 * @brief SYSCFG_PADHYS Register Bit Definition
 */

#define SYSCFG_PADHYS_I2C1MODESEL_SHIFT                 (16)
#define SYSCFG_PADHYS_I2C1MODESEL_MASK                  (0x01U << SYSCFG_PADHYS_I2C1MODESEL_SHIFT)
#define SYSCFG_PADHYS_I2C1MODESEL(x)                    (((uint32_t)(((uint32_t)(x)) << SYSCFG_PADHYS_I2C1MODESEL_SHIFT)) & SYSCFG_PADHYS_I2C1MODESEL_MASK)

/*!
 * @}
 */ /* end of group SYSCFG_Register_Masks */
/******************************************************************************
 * SYSCFG Instance
 ******************************************************************************/

#define SYSCFG                ((SYSCFG_Type*)SYSCFG_BASE)

/*!
 * @}
 */ /* end of group SYSCFG_Peripheral_Access_Layer */

/*!
 * @addtogroup EXTI_Peripheral_Access_Layer EXTI Peripheral Access Layer
 *  @{
 */

/*******************************************************************************
 * EXTI Type
 ******************************************************************************/
typedef struct {
    __IO uint32_t IMR;                                                            ///< Interrupt mask register                      offset: 0x00
    __IO uint32_t EMR;                                                            ///< Event mask register                          offset: 0x04
    __IO uint32_t RTSR;                                                           ///< Rising trigger selection register            offset: 0x08
    __IO uint32_t FTSR;                                                           ///< Falling trigger selection register           offset: 0x0C
    __IO uint32_t SWIER;                                                          ///< Software interrupt event register            offset: 0x10
    __IO uint32_t PR;                                                             ///< Pending register                             offset: 0x14
} EXTI_Type;

/*!
 * @addtogroup EXTI_Register_Masks Register Masks
 * @{ */

/*!
 * @brief EXTI_IMR Register Bit Definition
 */

#define EXTI_IMR_IMR17_SHIFT                            (17)
#define EXTI_IMR_IMR17_MASK                             (0x01U << EXTI_IMR_IMR17_SHIFT)
#define EXTI_IMR_IMR17(x)                               (((uint32_t)(((uint32_t)(x)) << EXTI_IMR_IMR17_SHIFT)) & EXTI_IMR_IMR17_MASK)

#define EXTI_IMR_IMR16_SHIFT                            (16)
#define EXTI_IMR_IMR16_MASK                             (0x01U << EXTI_IMR_IMR16_SHIFT)
#define EXTI_IMR_IMR16(x)                               (((uint32_t)(((uint32_t)(x)) << EXTI_IMR_IMR16_SHIFT)) & EXTI_IMR_IMR16_MASK)

#define EXTI_IMR_IMR15_SHIFT                            (15)
#define EXTI_IMR_IMR15_MASK                             (0x01U << EXTI_IMR_IMR15_SHIFT)
#define EXTI_IMR_IMR15(x)                               (((uint32_t)(((uint32_t)(x)) << EXTI_IMR_IMR15_SHIFT)) & EXTI_IMR_IMR15_MASK)

#define EXTI_IMR_IMR14_SHIFT                            (14)
#define EXTI_IMR_IMR14_MASK                             (0x01U << EXTI_IMR_IMR14_SHIFT)
#define EXTI_IMR_IMR14(x)                               (((uint32_t)(((uint32_t)(x)) << EXTI_IMR_IMR14_SHIFT)) & EXTI_IMR_IMR14_MASK)

#define EXTI_IMR_IMR13_SHIFT                            (13)
#define EXTI_IMR_IMR13_MASK                             (0x01U << EXTI_IMR_IMR13_SHIFT)
#define EXTI_IMR_IMR13(x)                               (((uint32_t)(((uint32_t)(x)) << EXTI_IMR_IMR13_SHIFT)) & EXTI_IMR_IMR13_MASK)

#define EXTI_IMR_IMR12_SHIFT                            (12)
#define EXTI_IMR_IMR12_MASK                             (0x01U << EXTI_IMR_IMR12_SHIFT)
#define EXTI_IMR_IMR12(x)                               (((uint32_t)(((uint32_t)(x)) << EXTI_IMR_IMR12_SHIFT)) & EXTI_IMR_IMR12_MASK)

#define EXTI_IMR_IMR11_SHIFT                            (11)
#define EXTI_IMR_IMR11_MASK                             (0x01U << EXTI_IMR_IMR11_SHIFT)
#define EXTI_IMR_IMR11(x)                               (((uint32_t)(((uint32_t)(x)) << EXTI_IMR_IMR11_SHIFT)) & EXTI_IMR_IMR11_MASK)

#define EXTI_IMR_IMR10_SHIFT                            (10)
#define EXTI_IMR_IMR10_MASK                             (0x01U << EXTI_IMR_IMR10_SHIFT)
#define EXTI_IMR_IMR10(x)                               (((uint32_t)(((uint32_t)(x)) << EXTI_IMR_IMR10_SHIFT)) & EXTI_IMR_IMR10_MASK)

#define EXTI_IMR_IMR9_SHIFT                             (9)
#define EXTI_IMR_IMR9_MASK                              (0x01U << EXTI_IMR_IMR9_SHIFT)
#define EXTI_IMR_IMR9(x)                                (((uint32_t)(((uint32_t)(x)) << EXTI_IMR_IMR9_SHIFT)) & EXTI_IMR_IMR9_MASK)

#define EXTI_IMR_IMR8_SHIFT                             (8)
#define EXTI_IMR_IMR8_MASK                              (0x01U << EXTI_IMR_IMR8_SHIFT)
#define EXTI_IMR_IMR8(x)                                (((uint32_t)(((uint32_t)(x)) << EXTI_IMR_IMR8_SHIFT)) & EXTI_IMR_IMR8_MASK)

#define EXTI_IMR_IMR7_SHIFT                             (7)
#define EXTI_IMR_IMR7_MASK                              (0x01U << EXTI_IMR_IMR7_SHIFT)
#define EXTI_IMR_IMR7(x)                                (((uint32_t)(((uint32_t)(x)) << EXTI_IMR_IMR7_SHIFT)) & EXTI_IMR_IMR7_MASK)

#define EXTI_IMR_IMR6_SHIFT                             (6)
#define EXTI_IMR_IMR6_MASK                              (0x01U << EXTI_IMR_IMR6_SHIFT)
#define EXTI_IMR_IMR6(x)                                (((uint32_t)(((uint32_t)(x)) << EXTI_IMR_IMR6_SHIFT)) & EXTI_IMR_IMR6_MASK)

#define EXTI_IMR_IMR5_SHIFT                             (5)
#define EXTI_IMR_IMR5_MASK                              (0x01U << EXTI_IMR_IMR5_SHIFT)
#define EXTI_IMR_IMR5(x)                                (((uint32_t)(((uint32_t)(x)) << EXTI_IMR_IMR5_SHIFT)) & EXTI_IMR_IMR5_MASK)

#define EXTI_IMR_IMR4_SHIFT                             (4)
#define EXTI_IMR_IMR4_MASK                              (0x01U << EXTI_IMR_IMR4_SHIFT)
#define EXTI_IMR_IMR4(x)                                (((uint32_t)(((uint32_t)(x)) << EXTI_IMR_IMR4_SHIFT)) & EXTI_IMR_IMR4_MASK)

#define EXTI_IMR_IMR3_SHIFT                             (3)
#define EXTI_IMR_IMR3_MASK                              (0x01U << EXTI_IMR_IMR3_SHIFT)
#define EXTI_IMR_IMR3(x)                                (((uint32_t)(((uint32_t)(x)) << EXTI_IMR_IMR3_SHIFT)) & EXTI_IMR_IMR3_MASK)

#define EXTI_IMR_IMR2_SHIFT                             (2)
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

#define EXTI_PR_PR8_SHIFT                               (8)
#define EXTI_PR_PR8_MASK                                (0x01U << EXTI_PR_PR8_SHIFT)
#define EXTI_PR_PR8(x)                                  (((uint32_t)(((uint32_t)(x)) << EXTI_PR_PR8_SHIFT)) & EXTI_PR_PR8_MASK)

#define EXTI_PR_PR7_SHIFT                               (7)
#define EXTI_PR_PR7_MASK                                (0x01U << EXTI_PR_PR7_SHIFT)
#define EXTI_PR_PR7(x)                                  (((uint32_t)(((uint32_t)(x)) << EXTI_PR_PR7_SHIFT)) & EXTI_PR_PR7_MASK)

#define EXTI_PR_PR6_SHIFT                               (6)
#define EXTI_PR_PR6_MASK                                (0x01U << EXTI_PR_PR6_SHIFT)
#define EXTI_PR_PR6(x)                                  (((uint32_t)(((uint32_t)(x)) << EXTI_PR_PR6_SHIFT)) & EXTI_PR_PR6_MASK)

#define EXTI_PR_PR5_SHIFT                               (5)
#define EXTI_PR_PR5_MASK                                (0x01U << EXTI_PR_PR5_SHIFT)
#define EXTI_PR_PR5(x)                                  (((uint32_t)(((uint32_t)(x)) << EXTI_PR_PR5_SHIFT)) & EXTI_PR_PR5_MASK)

#define EXTI_PR_PR4_SHIFT                               (4)
#define EXTI_PR_PR4_MASK                                (0x01U << EXTI_PR_PR4_SHIFT)
#define EXTI_PR_PR4(x)                                  (((uint32_t)(((uint32_t)(x)) << EXTI_PR_PR4_SHIFT)) & EXTI_PR_PR4_MASK)

#define EXTI_PR_PR3_SHIFT                               (3)
#define EXTI_PR_PR3_MASK                                (0x01U << EXTI_PR_PR3_SHIFT)
#define EXTI_PR_PR3(x)                                  (((uint32_t)(((uint32_t)(x)) << EXTI_PR_PR3_SHIFT)) & EXTI_PR_PR3_MASK)

#define EXTI_PR_PR2_SHIFT                               (2)
#define EXTI_PR_PR2_MASK                                (0x01U << EXTI_PR_PR2_SHIFT)
#define EXTI_PR_PR2(x)                                  (((uint32_t)(((uint32_t)(x)) << EXTI_PR_PR2_SHIFT)) & EXTI_PR_PR2_MASK)

#define EXTI_PR_PR1_SHIFT                               (1)
#define EXTI_PR_PR1_MASK                                (0x01U << EXTI_PR_PR1_SHIFT)
#define EXTI_PR_PR1(x)                                  (((uint32_t)(((uint32_t)(x)) << EXTI_PR_PR1_SHIFT)) & EXTI_PR_PR1_MASK)

#define EXTI_PR_PR0_SHIFT                               (0)
#define EXTI_PR_PR0_MASK                                (0x01U << EXTI_PR_PR0_SHIFT)
#define EXTI_PR_PR0(x)                                  (((uint32_t)(((uint32_t)(x)) << EXTI_PR_PR0_SHIFT)) & EXTI_PR_PR0_MASK)

/*!
 * @}
 */ /* end of group EXTI_Register_Masks */
/******************************************************************************
 * EXTI Instance
 ******************************************************************************/

#define EXTI                ((EXTI_Type*)EXTI_BASE)

/*!
 * @}
 */ /* end of group EXTI_Peripheral_Access_Layer */

/*!
 * @addtogroup FLASH_Peripheral_Access_Layer FLASH Peripheral Access Layer
 *  @{
 */

/*******************************************************************************
 * FLASH Type
 ******************************************************************************/
typedef struct {
    __IO uint32_t ACR;                                                            ///< Flash access control register                offset: 0x00
    __IO uint32_t KEYR;                                                           ///< Flash key                                    offset: 0x04
    __IO uint32_t OPTKEYR;                                                        ///< Option byte key                              offset: 0x08
    __IO uint32_t SR;                                                             ///< Flash status register                        offset: 0x0C
    __IO uint32_t CR;                                                             ///< Flash control register                       offset: 0x10
    __IO uint32_t AR;                                                             ///< Flash address register                       offset: 0x14
    __IO uint32_t Reserved0[1];                                                   ///< Reserved
    __IO uint32_t OBR;                                                            ///< Option byte register                         offset: 0x1c
    __IO uint32_t WRPR;                                                           ///< Write protect register                       offset: 0x20
} FLASH_Type;

/*!
 * @addtogroup FLASH_Register_Masks Register Masks
 * @{ */

/*!
 * @brief FLASH_ACR Register Bit Definition
 */

#define FLASH_ACR_PRFTBS_SHIFT                          (5)
#define FLASH_ACR_PRFTBS_MASK                           (0x01U << FLASH_ACR_PRFTBS_SHIFT)
#define FLASH_ACR_PRFTBS(x)                             (((uint32_t)(((uint32_t)(x)) << FLASH_ACR_PRFTBS_SHIFT)) & FLASH_ACR_PRFTBS_MASK)

#define FLASH_ACR_PRFTBE_SHIFT                          (4)
#define FLASH_ACR_PRFTBE_MASK                           (0x01U << FLASH_ACR_PRFTBE_SHIFT)
#define FLASH_ACR_PRFTBE(x)                             (((uint32_t)(((uint32_t)(x)) << FLASH_ACR_PRFTBE_SHIFT)) & FLASH_ACR_PRFTBE_MASK)

#define FLASH_ACR_HLFCYA_SHIFT                          (3)
#define FLASH_ACR_HLFCYA_MASK                           (0x01U << FLASH_ACR_HLFCYA_SHIFT)
#define FLASH_ACR_HLFCYA(x)                             (((uint32_t)(((uint32_t)(x)) << FLASH_ACR_HLFCYA_SHIFT)) & FLASH_ACR_HLFCYA_MASK)

#define FLASH_ACR_LATENCY_SHIFT                         (0)
#define FLASH_ACR_LATENCY_MASK                          (0x07U << FLASH_ACR_LATENCY_SHIFT)
#define FLASH_ACR_LATENCY(x)                            (((uint32_t)(((uint32_t)(x)) << FLASH_ACR_LATENCY_SHIFT)) & FLASH_ACR_LATENCY_MASK)

/*!
 * @brief FLASH_KEYR Register Bit Definition
 */

#define FLASH_KEYR_FKEYR_SHIFT                          (0)
#define FLASH_KEYR_FKEYR_MASK                           (0xFFFFFFFFU << FLASH_KEYR_FKEYR_SHIFT)
#define FLASH_KEYR_FKEYR(x)                             (((uint32_t)(((uint32_t)(x)) << FLASH_KEYR_FKEYR_SHIFT)) & FLASH_KEYR_FKEYR_MASK)

/*!
 * @brief FLASH_OPTKEYR Register Bit Definition
 */

#define FLASH_OPTKEYR_OPTKEYR_SHIFT                     (0)
#define FLASH_OPTKEYR_OPTKEYR_MASK                      (0xFFFFFFFFU << FLASH_OPTKEYR_OPTKEYR_SHIFT)
#define FLASH_OPTKEYR_OPTKEYR(x)                        (((uint32_t)(((uint32_t)(x)) << FLASH_OPTKEYR_OPTKEYR_SHIFT)) & FLASH_OPTKEYR_OPTKEYR_MASK)

/*!
 * @brief FLASH_SR Register Bit Definition
 */

#define FLASH_SR_EOP_SHIFT                              (5)
#define FLASH_SR_EOP_MASK                               (0x01U << FLASH_SR_EOP_SHIFT)
#define FLASH_SR_EOP(x)                                 (((uint32_t)(((uint32_t)(x)) << FLASH_SR_EOP_SHIFT)) & FLASH_SR_EOP_MASK)

#define FLASH_SR_WRPRTERR_SHIFT                         (4)
#define FLASH_SR_WRPRTERR_MASK                          (0x01U << FLASH_SR_WRPRTERR_SHIFT)
#define FLASH_SR_WRPRTERR(x)                            (((uint32_t)(((uint32_t)(x)) << FLASH_SR_WRPRTERR_SHIFT)) & FLASH_SR_WRPRTERR_MASK)

#define FLASH_SR_PGERR_SHIFT                            (2)
#define FLASH_SR_PGERR_MASK                             (0x01U << FLASH_SR_PGERR_SHIFT)
#define FLASH_SR_PGERR(x)                               (((uint32_t)(((uint32_t)(x)) << FLASH_SR_PGERR_SHIFT)) & FLASH_SR_PGERR_MASK)

#define FLASH_SR_BSY_SHIFT                              (0)
#define FLASH_SR_BSY_MASK                               (0x01U << FLASH_SR_BSY_SHIFT)
#define FLASH_SR_BSY(x)                                 (((uint32_t)(((uint32_t)(x)) << FLASH_SR_BSY_SHIFT)) & FLASH_SR_BSY_MASK)

/*!
 * @brief FLASH_CR Register Bit Definition
 */

#define FLASH_CR_EOPIE_SHIFT                            (12)
#define FLASH_CR_EOPIE_MASK                             (0x01U << FLASH_CR_EOPIE_SHIFT)
#define FLASH_CR_EOPIE(x)                               (((uint32_t)(((uint32_t)(x)) << FLASH_CR_EOPIE_SHIFT)) & FLASH_CR_EOPIE_MASK)

#define FLASH_CR_ERRIE_SHIFT                            (10)
#define FLASH_CR_ERRIE_MASK                             (0x01U << FLASH_CR_ERRIE_SHIFT)
#define FLASH_CR_ERRIE(x)                               (((uint32_t)(((uint32_t)(x)) << FLASH_CR_ERRIE_SHIFT)) & FLASH_CR_ERRIE_MASK)

#define FLASH_CR_OPTWRE_SHIFT                           (9)
#define FLASH_CR_OPTWRE_MASK                            (0x01U << FLASH_CR_OPTWRE_SHIFT)
#define FLASH_CR_OPTWRE(x)                              (((uint32_t)(((uint32_t)(x)) << FLASH_CR_OPTWRE_SHIFT)) & FLASH_CR_OPTWRE_MASK)

#define FLASH_CR_LOCK_SHIFT                             (7)
#define FLASH_CR_LOCK_MASK                              (0x01U << FLASH_CR_LOCK_SHIFT)
#define FLASH_CR_LOCK(x)                                (((uint32_t)(((uint32_t)(x)) << FLASH_CR_LOCK_SHIFT)) & FLASH_CR_LOCK_MASK)

#define FLASH_CR_STRT_SHIFT                             (6)
#define FLASH_CR_STRT_MASK                              (0x01U << FLASH_CR_STRT_SHIFT)
#define FLASH_CR_STRT(x)                                (((uint32_t)(((uint32_t)(x)) << FLASH_CR_STRT_SHIFT)) & FLASH_CR_STRT_MASK)

#define FLASH_CR_OPTER_SHIFT                            (5)
#define FLASH_CR_OPTER_MASK                             (0x01U << FLASH_CR_OPTER_SHIFT)
#define FLASH_CR_OPTER(x)                               (((uint32_t)(((uint32_t)(x)) << FLASH_CR_OPTER_SHIFT)) & FLASH_CR_OPTER_MASK)

#define FLASH_CR_OPTPG_SHIFT                            (4)
#define FLASH_CR_OPTPG_MASK                             (0x01U << FLASH_CR_OPTPG_SHIFT)
#define FLASH_CR_OPTPG(x)                               (((uint32_t)(((uint32_t)(x)) << FLASH_CR_OPTPG_SHIFT)) & FLASH_CR_OPTPG_MASK)

#define FLASH_CR_MER_SHIFT                              (2)
#define FLASH_CR_MER_MASK                               (0x01U << FLASH_CR_MER_SHIFT)
#define FLASH_CR_MER(x)                                 (((uint32_t)(((uint32_t)(x)) << FLASH_CR_MER_SHIFT)) & FLASH_CR_MER_MASK)

#define FLASH_CR_PER_SHIFT                              (1)
#define FLASH_CR_PER_MASK                               (0x01U << FLASH_CR_PER_SHIFT)
#define FLASH_CR_PER(x)                                 (((uint32_t)(((uint32_t)(x)) << FLASH_CR_PER_SHIFT)) & FLASH_CR_PER_MASK)

#define FLASH_CR_PG_SHIFT                               (0)
#define FLASH_CR_PG_MASK                                (0x01U << FLASH_CR_PG_SHIFT)
#define FLASH_CR_PG(x)                                  (((uint32_t)(((uint32_t)(x)) << FLASH_CR_PG_SHIFT)) & FLASH_CR_PG_MASK)

/*!
 * @brief FLASH_AR Register Bit Definition
 */

#define FLASH_AR_FAR_SHIFT                              (0)
#define FLASH_AR_FAR_MASK                               (0xFFFFFFFFU << FLASH_AR_FAR_SHIFT)
#define FLASH_AR_FAR(x)                                 (((uint32_t)(((uint32_t)(x)) << FLASH_AR_FAR_SHIFT)) & FLASH_AR_FAR_MASK)

/*!
 * @brief FLASH_OBR Register Bit Definition
 */

#define FLASH_OBR_DATA1_SHIFT                           (18)
#define FLASH_OBR_DATA1_MASK                            (0xFFU << FLASH_OBR_DATA1_SHIFT)
#define FLASH_OBR_DATA1(x)                              (((uint32_t)(((uint32_t)(x)) << FLASH_OBR_DATA1_SHIFT)) & FLASH_OBR_DATA1_MASK)

#define FLASH_OBR_DATA0_SHIFT                           (10)
#define FLASH_OBR_DATA0_MASK                            (0xFFU << FLASH_OBR_DATA0_SHIFT)
#define FLASH_OBR_DATA0(x)                              (((uint32_t)(((uint32_t)(x)) << FLASH_OBR_DATA0_SHIFT)) & FLASH_OBR_DATA0_MASK)

#define FLASH_OBR_NBOOT1_SHIFT                          (6)
#define FLASH_OBR_NBOOT1_MASK                           (0x01U << FLASH_OBR_NBOOT1_SHIFT)
#define FLASH_OBR_NBOOT1(x)                             (((uint32_t)(((uint32_t)(x)) << FLASH_OBR_NBOOT1_SHIFT)) & FLASH_OBR_NBOOT1_MASK)

#define FLASH_OBR_NRSTSTDBY_SHIFT                       (4)
#define FLASH_OBR_NRSTSTDBY_MASK                        (0x01U << FLASH_OBR_NRSTSTDBY_SHIFT)
#define FLASH_OBR_NRSTSTDBY(x)                          (((uint32_t)(((uint32_t)(x)) << FLASH_OBR_NRSTSTDBY_SHIFT)) & FLASH_OBR_NRSTSTDBY_MASK)

#define FLASH_OBR_NRSTSTOP_SHIFT                        (3)
#define FLASH_OBR_NRSTSTOP_MASK                         (0x01U << FLASH_OBR_NRSTSTOP_SHIFT)
#define FLASH_OBR_NRSTSTOP(x)                           (((uint32_t)(((uint32_t)(x)) << FLASH_OBR_NRSTSTOP_SHIFT)) & FLASH_OBR_NRSTSTOP_MASK)

#define FLASH_OBR_WDGSW_SHIFT                           (2)
#define FLASH_OBR_WDGSW_MASK                            (0x01U << FLASH_OBR_WDGSW_SHIFT)
#define FLASH_OBR_WDGSW(x)                              (((uint32_t)(((uint32_t)(x)) << FLASH_OBR_WDGSW_SHIFT)) & FLASH_OBR_WDGSW_MASK)

#define FLASH_OBR_RDPRT_SHIFT                           (1)
#define FLASH_OBR_RDPRT_MASK                            (0x01U << FLASH_OBR_RDPRT_SHIFT)
#define FLASH_OBR_RDPRT(x)                              (((uint32_t)(((uint32_t)(x)) << FLASH_OBR_RDPRT_SHIFT)) & FLASH_OBR_RDPRT_MASK)

#define FLASH_OBR_OPTERR_SHIFT                          (0)
#define FLASH_OBR_OPTERR_MASK                           (0x01U << FLASH_OBR_OPTERR_SHIFT)
#define FLASH_OBR_OPTERR(x)                             (((uint32_t)(((uint32_t)(x)) << FLASH_OBR_OPTERR_SHIFT)) & FLASH_OBR_OPTERR_MASK)

/*!
 * @brief FLASH_WRPR Register Bit Definition
 */

#define FLASH_WRPR_WRP_SHIFT                            (0)
#define FLASH_WRPR_WRP_MASK                             (0x0FU << FLASH_WRPR_WRP_SHIFT)
#define FLASH_WRPR_WRP(x)                               (((uint32_t)(((uint32_t)(x)) << FLASH_WRPR_WRP_SHIFT)) & FLASH_WRPR_WRP_MASK)

/*!
 * @}
 */ /* end of group FLASH_Register_Masks */
/******************************************************************************
 * FLASH Instance
 ******************************************************************************/

#define FLASH                ((FLASH_Type*)FLASH_BASE)

/*!
 * @}
 */ /* end of group FLASH_Peripheral_Access_Layer */

/*!
 * @addtogroup GPIO_Peripheral_Access_Layer GPIO Peripheral Access Layer
 *  @{
 */

/*******************************************************************************
 * GPIO Type
 ******************************************************************************/
typedef struct {
    __IO uint32_t CRL;                                                            ///< configuration low register                   offset: 0x00
    __IO uint32_t CRH;                                                            ///< configuration high register                  offset: 0x04
    __IO uint32_t IDR;                                                            ///< input data register                          offset: 0x08
    __IO uint32_t ODR;                                                            ///< output data register                         offset: 0x0C
    __IO uint32_t BSRR;                                                           ///< bit set/reset register                       offset: 0x10
    __IO uint32_t BRR;                                                            ///< bit reset register                           offset: 0x14
    __IO uint32_t LCKR;                                                           ///< Port configuration lock register             offset: 0x18
    __IO uint32_t DCR;                                                            ///< Port output open drain control register      offset: 0x1C
    __IO uint32_t AFRL;                                                           ///< Port Multiplexing Function Low Register      offset: 0x20
    __IO uint32_t AFRH;                                                           ///< Port Multiplexing Function High Register     offset: 0x24
} GPIO_Type;

/*!
 * @addtogroup GPIO_Register_Masks Register Masks
 * @{ */

/*!
 * @brief GPIO_CRL Register Bit Definition
 */

#define GPIO_CRL_CNF7_SHIFT                             (30)
#define GPIO_CRL_CNF7_MASK                              (0x03U << GPIO_CRL_CNF7_SHIFT)
#define GPIO_CRL_CNF7(x)                                (((uint32_t)(((uint32_t)(x)) << GPIO_CRL_CNF7_SHIFT)) & GPIO_CRL_CNF7_MASK)

#define GPIO_CRL_MODE7_SHIFT                            (28)
#define GPIO_CRL_MODE7_MASK                             (0x03U << GPIO_CRL_MODE7_SHIFT)
#define GPIO_CRL_MODE7(x)                               (((uint32_t)(((uint32_t)(x)) << GPIO_CRL_MODE7_SHIFT)) & GPIO_CRL_MODE7_MASK)

#define GPIO_CRL_CNF6_SHIFT                             (26)
#define GPIO_CRL_CNF6_MASK                              (0x03U << GPIO_CRL_CNF6_SHIFT)
#define GPIO_CRL_CNF6(x)                                (((uint32_t)(((uint32_t)(x)) << GPIO_CRL_CNF6_SHIFT)) & GPIO_CRL_CNF6_MASK)

#define GPIO_CRL_MODE6_SHIFT                            (24)
#define GPIO_CRL_MODE6_MASK                             (0x03U << GPIO_CRL_MODE6_SHIFT)
#define GPIO_CRL_MODE6(x)                               (((uint32_t)(((uint32_t)(x)) << GPIO_CRL_MODE6_SHIFT)) & GPIO_CRL_MODE6_MASK)

#define GPIO_CRL_CNF5_SHIFT                             (22)
#define GPIO_CRL_CNF5_MASK                              (0x03U << GPIO_CRL_CNF5_SHIFT)
#define GPIO_CRL_CNF5(x)                                (((uint32_t)(((uint32_t)(x)) << GPIO_CRL_CNF5_SHIFT)) & GPIO_CRL_CNF5_MASK)

#define GPIO_CRL_MODE5_SHIFT                            (20)
#define GPIO_CRL_MODE5_MASK                             (0x03U << GPIO_CRL_MODE5_SHIFT)
#define GPIO_CRL_MODE5(x)                               (((uint32_t)(((uint32_t)(x)) << GPIO_CRL_MODE5_SHIFT)) & GPIO_CRL_MODE5_MASK)

#define GPIO_CRL_CNF4_SHIFT                             (18)
#define GPIO_CRL_CNF4_MASK                              (0x03U << GPIO_CRL_CNF4_SHIFT)
#define GPIO_CRL_CNF4(x)                                (((uint32_t)(((uint32_t)(x)) << GPIO_CRL_CNF4_SHIFT)) & GPIO_CRL_CNF4_MASK)

#define GPIO_CRL_MODE4_SHIFT                            (16)
#define GPIO_CRL_MODE4_MASK                             (0x03U << GPIO_CRL_MODE4_SHIFT)
#define GPIO_CRL_MODE4(x)                               (((uint32_t)(((uint32_t)(x)) << GPIO_CRL_MODE4_SHIFT)) & GPIO_CRL_MODE4_MASK)

#define GPIO_CRL_CNF3_SHIFT                             (14)
#define GPIO_CRL_CNF3_MASK                              (0x03U << GPIO_CRL_CNF3_SHIFT)
#define GPIO_CRL_CNF3(x)                                (((uint32_t)(((uint32_t)(x)) << GPIO_CRL_CNF3_SHIFT)) & GPIO_CRL_CNF3_MASK)

#define GPIO_CRL_MODE3_SHIFT                            (12)
#define GPIO_CRL_MODE3_MASK                             (0x03U << GPIO_CRL_MODE3_SHIFT)
#define GPIO_CRL_MODE3(x)                               (((uint32_t)(((uint32_t)(x)) << GPIO_CRL_MODE3_SHIFT)) & GPIO_CRL_MODE3_MASK)

#define GPIO_CRL_CNF2_SHIFT                             (10)
#define GPIO_CRL_CNF2_MASK                              (0x03U << GPIO_CRL_CNF2_SHIFT)
#define GPIO_CRL_CNF2(x)                                (((uint32_t)(((uint32_t)(x)) << GPIO_CRL_CNF2_SHIFT)) & GPIO_CRL_CNF2_MASK)

#define GPIO_CRL_MODE2_SHIFT                            (8)
#define GPIO_CRL_MODE2_MASK                             (0x03U << GPIO_CRL_MODE2_SHIFT)
#define GPIO_CRL_MODE2(x)                               (((uint32_t)(((uint32_t)(x)) << GPIO_CRL_MODE2_SHIFT)) & GPIO_CRL_MODE2_MASK)

#define GPIO_CRL_CNF1_SHIFT                             (6)
#define GPIO_CRL_CNF1_MASK                              (0x03U << GPIO_CRL_CNF1_SHIFT)
#define GPIO_CRL_CNF1(x)                                (((uint32_t)(((uint32_t)(x)) << GPIO_CRL_CNF1_SHIFT)) & GPIO_CRL_CNF1_MASK)

#define GPIO_CRL_MODE1_SHIFT                            (4)
#define GPIO_CRL_MODE1_MASK                             (0x03U << GPIO_CRL_MODE1_SHIFT)
#define GPIO_CRL_MODE1(x)                               (((uint32_t)(((uint32_t)(x)) << GPIO_CRL_MODE1_SHIFT)) & GPIO_CRL_MODE1_MASK)

#define GPIO_CRL_CNF0_SHIFT                             (2)
#define GPIO_CRL_CNF0_MASK                              (0x03U << GPIO_CRL_CNF0_SHIFT)
#define GPIO_CRL_CNF0(x)                                (((uint32_t)(((uint32_t)(x)) << GPIO_CRL_CNF0_SHIFT)) & GPIO_CRL_CNF0_MASK)

#define GPIO_CRL_MODE0_SHIFT                            (0)
#define GPIO_CRL_MODE0_MASK                             (0x03U << GPIO_CRL_MODE0_SHIFT)
#define GPIO_CRL_MODE0(x)                               (((uint32_t)(((uint32_t)(x)) << GPIO_CRL_MODE0_SHIFT)) & GPIO_CRL_MODE0_MASK)

/*!
 * @brief GPIO_CRH Register Bit Definition
 */

#define GPIO_CRH_CNF15_SHIFT                            (30)
#define GPIO_CRH_CNF15_MASK                             (0x03U << GPIO_CRH_CNF15_SHIFT)
#define GPIO_CRH_CNF15(x)                               (((uint32_t)(((uint32_t)(x)) << GPIO_CRH_CNF15_SHIFT)) & GPIO_CRH_CNF15_MASK)

#define GPIO_CRH_MODE15_SHIFT                           (28)
#define GPIO_CRH_MODE15_MASK                            (0x03U << GPIO_CRH_MODE15_SHIFT)
#define GPIO_CRH_MODE15(x)                              (((uint32_t)(((uint32_t)(x)) << GPIO_CRH_MODE15_SHIFT)) & GPIO_CRH_MODE15_MASK)

#define GPIO_CRH_CNF14_SHIFT                            (26)
#define GPIO_CRH_CNF14_MASK                             (0x03U << GPIO_CRH_CNF14_SHIFT)
#define GPIO_CRH_CNF14(x)                               (((uint32_t)(((uint32_t)(x)) << GPIO_CRH_CNF14_SHIFT)) & GPIO_CRH_CNF14_MASK)

#define GPIO_CRH_MODE14_SHIFT                           (24)
#define GPIO_CRH_MODE14_MASK                            (0x03U << GPIO_CRH_MODE14_SHIFT)
#define GPIO_CRH_MODE14(x)                              (((uint32_t)(((uint32_t)(x)) << GPIO_CRH_MODE14_SHIFT)) & GPIO_CRH_MODE14_MASK)

#define GPIO_CRH_CNF13_SHIFT                            (22)
#define GPIO_CRH_CNF13_MASK                             (0x03U << GPIO_CRH_CNF13_SHIFT)
#define GPIO_CRH_CNF13(x)                               (((uint32_t)(((uint32_t)(x)) << GPIO_CRH_CNF13_SHIFT)) & GPIO_CRH_CNF13_MASK)

#define GPIO_CRH_MODE13_SHIFT                           (20)
#define GPIO_CRH_MODE13_MASK                            (0x03U << GPIO_CRH_MODE13_SHIFT)
#define GPIO_CRH_MODE13(x)                              (((uint32_t)(((uint32_t)(x)) << GPIO_CRH_MODE13_SHIFT)) & GPIO_CRH_MODE13_MASK)

#define GPIO_CRH_CNF12_SHIFT                            (18)
#define GPIO_CRH_CNF12_MASK                             (0x03U << GPIO_CRH_CNF12_SHIFT)
#define GPIO_CRH_CNF12(x)                               (((uint32_t)(((uint32_t)(x)) << GPIO_CRH_CNF12_SHIFT)) & GPIO_CRH_CNF12_MASK)

#define GPIO_CRH_MODE12_SHIFT                           (16)
#define GPIO_CRH_MODE12_MASK                            (0x03U << GPIO_CRH_MODE12_SHIFT)
#define GPIO_CRH_MODE12(x)                              (((uint32_t)(((uint32_t)(x)) << GPIO_CRH_MODE12_SHIFT)) & GPIO_CRH_MODE12_MASK)

#define GPIO_CRH_CNF11_SHIFT                            (14)
#define GPIO_CRH_CNF11_MASK                             (0x03U << GPIO_CRH_CNF11_SHIFT)
#define GPIO_CRH_CNF11(x)                               (((uint32_t)(((uint32_t)(x)) << GPIO_CRH_CNF11_SHIFT)) & GPIO_CRH_CNF11_MASK)

#define GPIO_CRH_MODE11_SHIFT                           (12)
#define GPIO_CRH_MODE11_MASK                            (0x03U << GPIO_CRH_MODE11_SHIFT)
#define GPIO_CRH_MODE11(x)                              (((uint32_t)(((uint32_t)(x)) << GPIO_CRH_MODE11_SHIFT)) & GPIO_CRH_MODE11_MASK)

#define GPIO_CRH_CNF10_SHIFT                            (10)
#define GPIO_CRH_CNF10_MASK                             (0x03U << GPIO_CRH_CNF10_SHIFT)
#define GPIO_CRH_CNF10(x)                               (((uint32_t)(((uint32_t)(x)) << GPIO_CRH_CNF10_SHIFT)) & GPIO_CRH_CNF10_MASK)

#define GPIO_CRH_MODE10_SHIFT                           (8)
#define GPIO_CRH_MODE10_MASK                            (0x03U << GPIO_CRH_MODE10_SHIFT)
#define GPIO_CRH_MODE10(x)                              (((uint32_t)(((uint32_t)(x)) << GPIO_CRH_MODE10_SHIFT)) & GPIO_CRH_MODE10_MASK)

#define GPIO_CRH_CNF9_SHIFT                             (6)
#define GPIO_CRH_CNF9_MASK                              (0x03U << GPIO_CRH_CNF9_SHIFT)
#define GPIO_CRH_CNF9(x)                                (((uint32_t)(((uint32_t)(x)) << GPIO_CRH_CNF9_SHIFT)) & GPIO_CRH_CNF9_MASK)

#define GPIO_CRH_MODE9_SHIFT                            (4)
#define GPIO_CRH_MODE9_MASK                             (0x03U << GPIO_CRH_MODE9_SHIFT)
#define GPIO_CRH_MODE9(x)                               (((uint32_t)(((uint32_t)(x)) << GPIO_CRH_MODE9_SHIFT)) & GPIO_CRH_MODE9_MASK)

#define GPIO_CRH_CNF8_SHIFT                             (2)
#define GPIO_CRH_CNF8_MASK                              (0x03U << GPIO_CRH_CNF8_SHIFT)
#define GPIO_CRH_CNF8(x)                                (((uint32_t)(((uint32_t)(x)) << GPIO_CRH_CNF8_SHIFT)) & GPIO_CRH_CNF8_MASK)

#define GPIO_CRH_MODE8_SHIFT                            (0)
#define GPIO_CRH_MODE8_MASK                             (0x03U << GPIO_CRH_MODE8_SHIFT)
#define GPIO_CRH_MODE8(x)                               (((uint32_t)(((uint32_t)(x)) << GPIO_CRH_MODE8_SHIFT)) & GPIO_CRH_MODE8_MASK)

/*!
 * @brief GPIO_IDR Register Bit Definition
 */

#define GPIO_IDR_IDR_SHIFT                              (0)
#define GPIO_IDR_IDR_MASK                               (0xFFFFU << GPIO_IDR_IDR_SHIFT)
#define GPIO_IDR_IDR(x)                                 (((uint32_t)(((uint32_t)(x)) << GPIO_IDR_IDR_SHIFT)) & GPIO_IDR_IDR_MASK)

/*!
 * @brief GPIO_ODR Register Bit Definition
 */

#define GPIO_ODR_ODR_SHIFT                              (0)
#define GPIO_ODR_ODR_MASK                               (0xFFFFU << GPIO_ODR_ODR_SHIFT)
#define GPIO_ODR_ODR(x)                                 (((uint32_t)(((uint32_t)(x)) << GPIO_ODR_ODR_SHIFT)) & GPIO_ODR_ODR_MASK)

/*!
 * @brief GPIO_BSRR Register Bit Definition
 */

#define GPIO_BSRR_BR15_SHIFT                            (31)
#define GPIO_BSRR_BR15_MASK                             (0x01U << GPIO_BSRR_BR15_SHIFT)
#define GPIO_BSRR_BR15(x)                               (((uint32_t)(((uint32_t)(x)) << GPIO_BSRR_BR15_SHIFT)) & GPIO_BSRR_BR15_MASK)

#define GPIO_BSRR_BR14_SHIFT                            (30)
#define GPIO_BSRR_BR14_MASK                             (0x01U << GPIO_BSRR_BR14_SHIFT)
#define GPIO_BSRR_BR14(x)                               (((uint32_t)(((uint32_t)(x)) << GPIO_BSRR_BR14_SHIFT)) & GPIO_BSRR_BR14_MASK)

#define GPIO_BSRR_BR13_SHIFT                            (29)
#define GPIO_BSRR_BR13_MASK                             (0x01U << GPIO_BSRR_BR13_SHIFT)
#define GPIO_BSRR_BR13(x)                               (((uint32_t)(((uint32_t)(x)) << GPIO_BSRR_BR13_SHIFT)) & GPIO_BSRR_BR13_MASK)

#define GPIO_BSRR_BR12_SHIFT                            (28)
#define GPIO_BSRR_BR12_MASK                             (0x01U << GPIO_BSRR_BR12_SHIFT)
#define GPIO_BSRR_BR12(x)                               (((uint32_t)(((uint32_t)(x)) << GPIO_BSRR_BR12_SHIFT)) & GPIO_BSRR_BR12_MASK)

#define GPIO_BSRR_BR11_SHIFT                            (27)
#define GPIO_BSRR_BR11_MASK                             (0x01U << GPIO_BSRR_BR11_SHIFT)
#define GPIO_BSRR_BR11(x)                               (((uint32_t)(((uint32_t)(x)) << GPIO_BSRR_BR11_SHIFT)) & GPIO_BSRR_BR11_MASK)

#define GPIO_BSRR_BR10_SHIFT                            (26)
#define GPIO_BSRR_BR10_MASK                             (0x01U << GPIO_BSRR_BR10_SHIFT)
#define GPIO_BSRR_BR10(x)                               (((uint32_t)(((uint32_t)(x)) << GPIO_BSRR_BR10_SHIFT)) & GPIO_BSRR_BR10_MASK)

#define GPIO_BSRR_BR9_SHIFT                             (25)
#define GPIO_BSRR_BR9_MASK                              (0x01U << GPIO_BSRR_BR9_SHIFT)
#define GPIO_BSRR_BR9(x)                                (((uint32_t)(((uint32_t)(x)) << GPIO_BSRR_BR9_SHIFT)) & GPIO_BSRR_BR9_MASK)

#define GPIO_BSRR_BR8_SHIFT                             (24)
#define GPIO_BSRR_BR8_MASK                              (0x01U << GPIO_BSRR_BR8_SHIFT)
#define GPIO_BSRR_BR8(x)                                (((uint32_t)(((uint32_t)(x)) << GPIO_BSRR_BR8_SHIFT)) & GPIO_BSRR_BR8_MASK)

#define GPIO_BSRR_BR7_SHIFT                             (23)
#define GPIO_BSRR_BR7_MASK                              (0x01U << GPIO_BSRR_BR7_SHIFT)
#define GPIO_BSRR_BR7(x)                                (((uint32_t)(((uint32_t)(x)) << GPIO_BSRR_BR7_SHIFT)) & GPIO_BSRR_BR7_MASK)

#define GPIO_BSRR_BR6_SHIFT                             (22)
#define GPIO_BSRR_BR6_MASK                              (0x01U << GPIO_BSRR_BR6_SHIFT)
#define GPIO_BSRR_BR6(x)                                (((uint32_t)(((uint32_t)(x)) << GPIO_BSRR_BR6_SHIFT)) & GPIO_BSRR_BR6_MASK)

#define GPIO_BSRR_BR5_SHIFT                             (21)
#define GPIO_BSRR_BR5_MASK                              (0x01U << GPIO_BSRR_BR5_SHIFT)
#define GPIO_BSRR_BR5(x)                                (((uint32_t)(((uint32_t)(x)) << GPIO_BSRR_BR5_SHIFT)) & GPIO_BSRR_BR5_MASK)

#define GPIO_BSRR_BR4_SHIFT                             (20)
#define GPIO_BSRR_BR4_MASK                              (0x01U << GPIO_BSRR_BR4_SHIFT)
#define GPIO_BSRR_BR4(x)                                (((uint32_t)(((uint32_t)(x)) << GPIO_BSRR_BR4_SHIFT)) & GPIO_BSRR_BR4_MASK)

#define GPIO_BSRR_BR3_SHIFT                             (19)
#define GPIO_BSRR_BR3_MASK                              (0x01U << GPIO_BSRR_BR3_SHIFT)
#define GPIO_BSRR_BR3(x)                                (((uint32_t)(((uint32_t)(x)) << GPIO_BSRR_BR3_SHIFT)) & GPIO_BSRR_BR3_MASK)

#define GPIO_BSRR_BR2_SHIFT                             (18)
#define GPIO_BSRR_BR2_MASK                              (0x01U << GPIO_BSRR_BR2_SHIFT)
#define GPIO_BSRR_BR2(x)                                (((uint32_t)(((uint32_t)(x)) << GPIO_BSRR_BR2_SHIFT)) & GPIO_BSRR_BR2_MASK)

#define GPIO_BSRR_BR1_SHIFT                             (17)
#define GPIO_BSRR_BR1_MASK                              (0x01U << GPIO_BSRR_BR1_SHIFT)
#define GPIO_BSRR_BR1(x)                                (((uint32_t)(((uint32_t)(x)) << GPIO_BSRR_BR1_SHIFT)) & GPIO_BSRR_BR1_MASK)

#define GPIO_BSRR_BR0_SHIFT                             (16)
#define GPIO_BSRR_BR0_MASK                              (0x01U << GPIO_BSRR_BR0_SHIFT)
#define GPIO_BSRR_BR0(x)                                (((uint32_t)(((uint32_t)(x)) << GPIO_BSRR_BR0_SHIFT)) & GPIO_BSRR_BR0_MASK)

#define GPIO_BSRR_BS15_SHIFT                            (15)
#define GPIO_BSRR_BS15_MASK                             (0x01U << GPIO_BSRR_BS15_SHIFT)
#define GPIO_BSRR_BS15(x)                               (((uint32_t)(((uint32_t)(x)) << GPIO_BSRR_BS15_SHIFT)) & GPIO_BSRR_BS15_MASK)

#define GPIO_BSRR_BS14_SHIFT                            (14)
#define GPIO_BSRR_BS14_MASK                             (0x01U << GPIO_BSRR_BS14_SHIFT)
#define GPIO_BSRR_BS14(x)                               (((uint32_t)(((uint32_t)(x)) << GPIO_BSRR_BS14_SHIFT)) & GPIO_BSRR_BS14_MASK)

#define GPIO_BSRR_BS13_SHIFT                            (13)
#define GPIO_BSRR_BS13_MASK                             (0x01U << GPIO_BSRR_BS13_SHIFT)
#define GPIO_BSRR_BS13(x)                               (((uint32_t)(((uint32_t)(x)) << GPIO_BSRR_BS13_SHIFT)) & GPIO_BSRR_BS13_MASK)

#define GPIO_BSRR_BS12_SHIFT                            (12)
#define GPIO_BSRR_BS12_MASK                             (0x01U << GPIO_BSRR_BS12_SHIFT)
#define GPIO_BSRR_BS12(x)                               (((uint32_t)(((uint32_t)(x)) << GPIO_BSRR_BS12_SHIFT)) & GPIO_BSRR_BS12_MASK)

#define GPIO_BSRR_BS11_SHIFT                            (11)
#define GPIO_BSRR_BS11_MASK                             (0x01U << GPIO_BSRR_BS11_SHIFT)
#define GPIO_BSRR_BS11(x)                               (((uint32_t)(((uint32_t)(x)) << GPIO_BSRR_BS11_SHIFT)) & GPIO_BSRR_BS11_MASK)

#define GPIO_BSRR_BS10_SHIFT                            (10)
#define GPIO_BSRR_BS10_MASK                             (0x01U << GPIO_BSRR_BS10_SHIFT)
#define GPIO_BSRR_BS10(x)                               (((uint32_t)(((uint32_t)(x)) << GPIO_BSRR_BS10_SHIFT)) & GPIO_BSRR_BS10_MASK)

#define GPIO_BSRR_BS9_SHIFT                             (9)
#define GPIO_BSRR_BS9_MASK                              (0x01U << GPIO_BSRR_BS9_SHIFT)
#define GPIO_BSRR_BS9(x)                                (((uint32_t)(((uint32_t)(x)) << GPIO_BSRR_BS9_SHIFT)) & GPIO_BSRR_BS9_MASK)

#define GPIO_BSRR_BS8_SHIFT                             (8)
#define GPIO_BSRR_BS8_MASK                              (0x01U << GPIO_BSRR_BS8_SHIFT)
#define GPIO_BSRR_BS8(x)                                (((uint32_t)(((uint32_t)(x)) << GPIO_BSRR_BS8_SHIFT)) & GPIO_BSRR_BS8_MASK)

#define GPIO_BSRR_BS7_SHIFT                             (7)
#define GPIO_BSRR_BS7_MASK                              (0x01U << GPIO_BSRR_BS7_SHIFT)
#define GPIO_BSRR_BS7(x)                                (((uint32_t)(((uint32_t)(x)) << GPIO_BSRR_BS7_SHIFT)) & GPIO_BSRR_BS7_MASK)

#define GPIO_BSRR_BS6_SHIFT                             (6)
#define GPIO_BSRR_BS6_MASK                              (0x01U << GPIO_BSRR_BS6_SHIFT)
#define GPIO_BSRR_BS6(x)                                (((uint32_t)(((uint32_t)(x)) << GPIO_BSRR_BS6_SHIFT)) & GPIO_BSRR_BS6_MASK)

#define GPIO_BSRR_BS5_SHIFT                             (5)
#define GPIO_BSRR_BS5_MASK                              (0x01U << GPIO_BSRR_BS5_SHIFT)
#define GPIO_BSRR_BS5(x)                                (((uint32_t)(((uint32_t)(x)) << GPIO_BSRR_BS5_SHIFT)) & GPIO_BSRR_BS5_MASK)

#define GPIO_BSRR_BS4_SHIFT                             (4)
#define GPIO_BSRR_BS4_MASK                              (0x01U << GPIO_BSRR_BS4_SHIFT)
#define GPIO_BSRR_BS4(x)                                (((uint32_t)(((uint32_t)(x)) << GPIO_BSRR_BS4_SHIFT)) & GPIO_BSRR_BS4_MASK)

#define GPIO_BSRR_BS3_SHIFT                             (3)
#define GPIO_BSRR_BS3_MASK                              (0x01U << GPIO_BSRR_BS3_SHIFT)
#define GPIO_BSRR_BS3(x)                                (((uint32_t)(((uint32_t)(x)) << GPIO_BSRR_BS3_SHIFT)) & GPIO_BSRR_BS3_MASK)

#define GPIO_BSRR_BS2_SHIFT                             (2)
#define GPIO_BSRR_BS2_MASK                              (0x01U << GPIO_BSRR_BS2_SHIFT)
#define GPIO_BSRR_BS2(x)                                (((uint32_t)(((uint32_t)(x)) << GPIO_BSRR_BS2_SHIFT)) & GPIO_BSRR_BS2_MASK)

#define GPIO_BSRR_BS1_SHIFT                             (1)
#define GPIO_BSRR_BS1_MASK                              (0x01U << GPIO_BSRR_BS1_SHIFT)
#define GPIO_BSRR_BS1(x)                                (((uint32_t)(((uint32_t)(x)) << GPIO_BSRR_BS1_SHIFT)) & GPIO_BSRR_BS1_MASK)

#define GPIO_BSRR_BS0_SHIFT                             (0)
#define GPIO_BSRR_BS0_MASK                              (0x01U << GPIO_BSRR_BS0_SHIFT)
#define GPIO_BSRR_BS0(x)                                (((uint32_t)(((uint32_t)(x)) << GPIO_BSRR_BS0_SHIFT)) & GPIO_BSRR_BS0_MASK)

/*!
 * @brief GPIO_BRR Register Bit Definition
 */

#define GPIO_BRR_BR15_SHIFT                             (15)
#define GPIO_BRR_BR15_MASK                              (0x01U << GPIO_BRR_BR15_SHIFT)
#define GPIO_BRR_BR15(x)                                (((uint32_t)(((uint32_t)(x)) << GPIO_BRR_BR15_SHIFT)) & GPIO_BRR_BR15_MASK)

#define GPIO_BRR_BR14_SHIFT                             (14)
#define GPIO_BRR_BR14_MASK                              (0x01U << GPIO_BRR_BR14_SHIFT)
#define GPIO_BRR_BR14(x)                                (((uint32_t)(((uint32_t)(x)) << GPIO_BRR_BR14_SHIFT)) & GPIO_BRR_BR14_MASK)

#define GPIO_BRR_BR13_SHIFT                             (13)
#define GPIO_BRR_BR13_MASK                              (0x01U << GPIO_BRR_BR13_SHIFT)
#define GPIO_BRR_BR13(x)                                (((uint32_t)(((uint32_t)(x)) << GPIO_BRR_BR13_SHIFT)) & GPIO_BRR_BR13_MASK)

#define GPIO_BRR_BR12_SHIFT                             (12)
#define GPIO_BRR_BR12_MASK                              (0x01U << GPIO_BRR_BR12_SHIFT)
#define GPIO_BRR_BR12(x)                                (((uint32_t)(((uint32_t)(x)) << GPIO_BRR_BR12_SHIFT)) & GPIO_BRR_BR12_MASK)

#define GPIO_BRR_BR11_SHIFT                             (11)
#define GPIO_BRR_BR11_MASK                              (0x01U << GPIO_BRR_BR11_SHIFT)
#define GPIO_BRR_BR11(x)                                (((uint32_t)(((uint32_t)(x)) << GPIO_BRR_BR11_SHIFT)) & GPIO_BRR_BR11_MASK)

#define GPIO_BRR_BR10_SHIFT                             (10)
#define GPIO_BRR_BR10_MASK                              (0x01U << GPIO_BRR_BR10_SHIFT)
#define GPIO_BRR_BR10(x)                                (((uint32_t)(((uint32_t)(x)) << GPIO_BRR_BR10_SHIFT)) & GPIO_BRR_BR10_MASK)

#define GPIO_BRR_BR9_SHIFT                              (9)
#define GPIO_BRR_BR9_MASK                               (0x01U << GPIO_BRR_BR9_SHIFT)
#define GPIO_BRR_BR9(x)                                 (((uint32_t)(((uint32_t)(x)) << GPIO_BRR_BR9_SHIFT)) & GPIO_BRR_BR9_MASK)

#define GPIO_BRR_BR8_SHIFT                              (8)
#define GPIO_BRR_BR8_MASK                               (0x01U << GPIO_BRR_BR8_SHIFT)
#define GPIO_BRR_BR8(x)                                 (((uint32_t)(((uint32_t)(x)) << GPIO_BRR_BR8_SHIFT)) & GPIO_BRR_BR8_MASK)

#define GPIO_BRR_BR7_SHIFT                              (7)
#define GPIO_BRR_BR7_MASK                               (0x01U << GPIO_BRR_BR7_SHIFT)
#define GPIO_BRR_BR7(x)                                 (((uint32_t)(((uint32_t)(x)) << GPIO_BRR_BR7_SHIFT)) & GPIO_BRR_BR7_MASK)

#define GPIO_BRR_BR6_SHIFT                              (6)
#define GPIO_BRR_BR6_MASK                               (0x01U << GPIO_BRR_BR6_SHIFT)
#define GPIO_BRR_BR6(x)                                 (((uint32_t)(((uint32_t)(x)) << GPIO_BRR_BR6_SHIFT)) & GPIO_BRR_BR6_MASK)

#define GPIO_BRR_BR5_SHIFT                              (5)
#define GPIO_BRR_BR5_MASK                               (0x01U << GPIO_BRR_BR5_SHIFT)
#define GPIO_BRR_BR5(x)                                 (((uint32_t)(((uint32_t)(x)) << GPIO_BRR_BR5_SHIFT)) & GPIO_BRR_BR5_MASK)

#define GPIO_BRR_BR4_SHIFT                              (4)
#define GPIO_BRR_BR4_MASK                               (0x01U << GPIO_BRR_BR4_SHIFT)
#define GPIO_BRR_BR4(x)                                 (((uint32_t)(((uint32_t)(x)) << GPIO_BRR_BR4_SHIFT)) & GPIO_BRR_BR4_MASK)

#define GPIO_BRR_BR3_SHIFT                              (3)
#define GPIO_BRR_BR3_MASK                               (0x01U << GPIO_BRR_BR3_SHIFT)
#define GPIO_BRR_BR3(x)                                 (((uint32_t)(((uint32_t)(x)) << GPIO_BRR_BR3_SHIFT)) & GPIO_BRR_BR3_MASK)

#define GPIO_BRR_BR2_SHIFT                              (2)
#define GPIO_BRR_BR2_MASK                               (0x01U << GPIO_BRR_BR2_SHIFT)
#define GPIO_BRR_BR2(x)                                 (((uint32_t)(((uint32_t)(x)) << GPIO_BRR_BR2_SHIFT)) & GPIO_BRR_BR2_MASK)

#define GPIO_BRR_BR1_SHIFT                              (1)
#define GPIO_BRR_BR1_MASK                               (0x01U << GPIO_BRR_BR1_SHIFT)
#define GPIO_BRR_BR1(x)                                 (((uint32_t)(((uint32_t)(x)) << GPIO_BRR_BR1_SHIFT)) & GPIO_BRR_BR1_MASK)

#define GPIO_BRR_BR0_SHIFT                              (0)
#define GPIO_BRR_BR0_MASK                               (0x01U << GPIO_BRR_BR0_SHIFT)
#define GPIO_BRR_BR0(x)                                 (((uint32_t)(((uint32_t)(x)) << GPIO_BRR_BR0_SHIFT)) & GPIO_BRR_BR0_MASK)

/*!
 * @brief GPIO_LCKR Register Bit Definition
 */

#define GPIO_LCKR_LCKK_SHIFT                            (16)
#define GPIO_LCKR_LCKK_MASK                             (0x01U << GPIO_LCKR_LCKK_SHIFT)
#define GPIO_LCKR_LCKK(x)                               (((uint32_t)(((uint32_t)(x)) << GPIO_LCKR_LCKK_SHIFT)) & GPIO_LCKR_LCKK_MASK)

#define GPIO_LCKR_LCK_SHIFT                             (0)
#define GPIO_LCKR_LCK_MASK                              (0xFFFFU << GPIO_LCKR_LCK_SHIFT)
#define GPIO_LCKR_LCK(x)                                (((uint32_t)(((uint32_t)(x)) << GPIO_LCKR_LCK_SHIFT)) & GPIO_LCKR_LCK_MASK)

/*!
 * @brief GPIO_DCR Register Bit Definition
 */

#define GPIO_DCR_PX15_SHIFT                             (30)
#define GPIO_DCR_PX15_MASK                              (0x03U << GPIO_DCR_PX15_SHIFT)
#define GPIO_DCR_PX15(x)                                (((uint32_t)(((uint32_t)(x)) << GPIO_DCR_PX15_SHIFT)) & GPIO_DCR_PX15_MASK)

#define GPIO_DCR_PX14_SHIFT                             (28)
#define GPIO_DCR_PX14_MASK                              (0x03U << GPIO_DCR_PX14_SHIFT)
#define GPIO_DCR_PX14(x)                                (((uint32_t)(((uint32_t)(x)) << GPIO_DCR_PX14_SHIFT)) & GPIO_DCR_PX14_MASK)

#define GPIO_DCR_PX13_SHIFT                             (26)
#define GPIO_DCR_PX13_MASK                              (0x03U << GPIO_DCR_PX13_SHIFT)
#define GPIO_DCR_PX13(x)                                (((uint32_t)(((uint32_t)(x)) << GPIO_DCR_PX13_SHIFT)) & GPIO_DCR_PX13_MASK)

#define GPIO_DCR_PX12_SHIFT                             (24)
#define GPIO_DCR_PX12_MASK                              (0x03U << GPIO_DCR_PX12_SHIFT)
#define GPIO_DCR_PX12(x)                                (((uint32_t)(((uint32_t)(x)) << GPIO_DCR_PX12_SHIFT)) & GPIO_DCR_PX12_MASK)

#define GPIO_DCR_PX11_SHIFT                             (22)
#define GPIO_DCR_PX11_MASK                              (0x03U << GPIO_DCR_PX11_SHIFT)
#define GPIO_DCR_PX11(x)                                (((uint32_t)(((uint32_t)(x)) << GPIO_DCR_PX11_SHIFT)) & GPIO_DCR_PX11_MASK)

#define GPIO_DCR_PX10_SHIFT                             (20)
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

#define GPIO_AFRL_AFR4_SHIFT                            (16)
#define GPIO_AFRL_AFR4_MASK                             (0x0FU << GPIO_AFRL_AFR4_SHIFT)
#define GPIO_AFRL_AFR4(x)                               (((uint32_t)(((uint32_t)(x)) << GPIO_AFRL_AFR4_SHIFT)) & GPIO_AFRL_AFR4_MASK)

#define GPIO_AFRL_AFR3_SHIFT                            (12)
#define GPIO_AFRL_AFR3_MASK                             (0x0FU << GPIO_AFRL_AFR3_SHIFT)
#define GPIO_AFRL_AFR3(x)                               (((uint32_t)(((uint32_t)(x)) << GPIO_AFRL_AFR3_SHIFT)) & GPIO_AFRL_AFR3_MASK)

#define GPIO_AFRL_AFR2_SHIFT                            (8)
#define GPIO_AFRL_AFR2_MASK                             (0x0FU << GPIO_AFRL_AFR2_SHIFT)
#define GPIO_AFRL_AFR2(x)                               (((uint32_t)(((uint32_t)(x)) << GPIO_AFRL_AFR2_SHIFT)) & GPIO_AFRL_AFR2_MASK)

#define GPIO_AFRL_AFR1_SHIFT                            (4)
#define GPIO_AFRL_AFR1_MASK                             (0x0FU << GPIO_AFRL_AFR1_SHIFT)
#define GPIO_AFRL_AFR1(x)                               (((uint32_t)(((uint32_t)(x)) << GPIO_AFRL_AFR1_SHIFT)) & GPIO_AFRL_AFR1_MASK)

#define GPIO_AFRL_AFR0_SHIFT                            (0)
#define GPIO_AFRL_AFR0_MASK                             (0x0FU << GPIO_AFRL_AFR0_SHIFT)
#define GPIO_AFRL_AFR0(x)                               (((uint32_t)(((uint32_t)(x)) << GPIO_AFRL_AFR0_SHIFT)) & GPIO_AFRL_AFR0_MASK)

/*!
 * @brief GPIO_AFRH Register Bit Definition
 */

#define GPIO_AFRH_AFR15_SHIFT                           (28)
#define GPIO_AFRH_AFR15_MASK                            (0x0FU << GPIO_AFRH_AFR15_SHIFT)
#define GPIO_AFRH_AFR15(x)                              (((uint32_t)(((uint32_t)(x)) << GPIO_AFRH_AFR15_SHIFT)) & GPIO_AFRH_AFR15_MASK)

#define GPIO_AFRH_AFR14_SHIFT                           (24)
#define GPIO_AFRH_AFR14_MASK                            (0x0FU << GPIO_AFRH_AFR14_SHIFT)
#define GPIO_AFRH_AFR14(x)                              (((uint32_t)(((uint32_t)(x)) << GPIO_AFRH_AFR14_SHIFT)) & GPIO_AFRH_AFR14_MASK)

#define GPIO_AFRH_AFR13_SHIFT                           (20)
#define GPIO_AFRH_AFR13_MASK                            (0x0FU << GPIO_AFRH_AFR13_SHIFT)
#define GPIO_AFRH_AFR13(x)                              (((uint32_t)(((uint32_t)(x)) << GPIO_AFRH_AFR13_SHIFT)) & GPIO_AFRH_AFR13_MASK)

#define GPIO_AFRH_AFR12_SHIFT                           (16)
#define GPIO_AFRH_AFR12_MASK                            (0x0FU << GPIO_AFRH_AFR12_SHIFT)
#define GPIO_AFRH_AFR12(x)                              (((uint32_t)(((uint32_t)(x)) << GPIO_AFRH_AFR12_SHIFT)) & GPIO_AFRH_AFR12_MASK)

#define GPIO_AFRH_AFR11_SHIFT                           (12)
#define GPIO_AFRH_AFR11_MASK                            (0x0FU << GPIO_AFRH_AFR11_SHIFT)
#define GPIO_AFRH_AFR11(x)                              (((uint32_t)(((uint32_t)(x)) << GPIO_AFRH_AFR11_SHIFT)) & GPIO_AFRH_AFR11_MASK)

#define GPIO_AFRH_AFR10_SHIFT                           (8)
#define GPIO_AFRH_AFR10_MASK                            (0x0FU << GPIO_AFRH_AFR10_SHIFT)
#define GPIO_AFRH_AFR10(x)                              (((uint32_t)(((uint32_t)(x)) << GPIO_AFRH_AFR10_SHIFT)) & GPIO_AFRH_AFR10_MASK)

#define GPIO_AFRH_AFR9_SHIFT                            (4)
#define GPIO_AFRH_AFR9_MASK                             (0x0FU << GPIO_AFRH_AFR9_SHIFT)
#define GPIO_AFRH_AFR9(x)                               (((uint32_t)(((uint32_t)(x)) << GPIO_AFRH_AFR9_SHIFT)) & GPIO_AFRH_AFR9_MASK)

#define GPIO_AFRH_AFR8_SHIFT                            (0)
#define GPIO_AFRH_AFR8_MASK                             (0x0FU << GPIO_AFRH_AFR8_SHIFT)
#define GPIO_AFRH_AFR8(x)                               (((uint32_t)(((uint32_t)(x)) << GPIO_AFRH_AFR8_SHIFT)) & GPIO_AFRH_AFR8_MASK)

/*!
 * @}
 */ /* end of group GPIO_Register_Masks */
/******************************************************************************
 * GPIO Instance
 ******************************************************************************/

#define GPIOA                ((GPIO_Type*)GPIOA_BASE)
#define GPIOB                ((GPIO_Type*)GPIOB_BASE)

/*!
 * @}
 */ /* end of group GPIO_Peripheral_Access_Layer */

/*!
 * @addtogroup I2C_Peripheral_Access_Layer I2C Peripheral Access Layer
 *  @{
 */
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
