UnsicentificLaLaLaLa/led-matrix/software/firmware/led-matrix_firmware/device/hal_device_registers.h

/*
 * Copyright 2022 MindMotion Microelectronics Co., Ltd.
 * All rights reserved.
 *
 * SPDX-License-Identifier: BSD-3-Clause
 */

#ifndef __HAL_DEVICE_REGISTER_H__
#define __HAL_DEVICE_REGISTER_H__


#include "mm32g0001a.h"
#include "mm32g0001a_features.h"
#include "system_mm32g0001a.h"

#endif /* __HAL_DEVICE_REGISTER_H__ */
